jrtaylor71/ESP32-DevKitC3-Simple-Thermostat-PCB/SCHEDULE_SYNC_INDEX.md

# Schedule Sync Documentation Index

**Version 1.5.001** | Complete bidirectional MQTT schedule synchronization  
**Last Updated**: May 2026

Note: Schedule synchronization behavior remains compatible in v1.5.001. New US/EU regional HVAC controls are documented in README.md, DOCUMENTATION.md, and USER_MANUAL.md.

---

## 📖 Documentation Guide

### For Different Audiences

#### 👤 **I'm a First-Time User**
Start here for quickest setup:
1. [MQTT_SCHEDULE_QUICKSTART.md](MQTT_SCHEDULE_QUICKSTART.md) ⏱️ 5 minutes
   - Copy-paste setup commands
   - Verification checklist
   - Troubleshooting links

#### 👨‍💻 **I'm Setting Up Home Assistant**
Full user guide with detailed instructions:
1. [README.md § Home Assistant Integration](README.md#-home-assistant-integration)
   - Feature overview
   - Setup steps
   - Multi-device support

2. [USER_MANUAL.md § Schedule Synchronization](USER_MANUAL.md#schedule-synchronization-) 
   - Detailed setup (5 steps)
   - What gets created (helper breakdown)
   - How to edit schedules
   - Multi-thermostat guide

#### 🔧 **I'm a Developer/Integrator**
Technical deep-dive:
1. [DEVELOPMENT_GUIDE.md § MQTT 7-Day Schedule Architecture](DEVELOPMENT_GUIDE.md#mqtt-7-day-schedule-architecture-)
   - Firmware C++ structures
   - Inbound/outbound handlers
   - Day index conversion logic
   - HA automation code

2. [MQTT_SCHEDULE_SYNC.md](MQTT_SCHEDULE_SYNC.md)
   - Complete technical reference
   - All MQTT formats (topics, payloads)
   - Data flow diagrams
   - Advanced configuration

#### 🐛 **I'm Having Issues**
Problem-solving guide:
1. [MQTT_SCHEDULE_SYNC.md § Troubleshooting](MQTT_SCHEDULE_SYNC.md#troubleshooting)
   - 10+ common issues
   - Solutions for each
   - Debug commands
   - Verification steps

---

## 📚 Complete Documentation Map

### Core Documentation Files

| File | Size | Focus | Audience |
|---|---|---|---|
| [README.md](README.md) | 15K | Product overview, features, HA integration | Everyone |
| [USER_MANUAL.md](USER_MANUAL.md) | 40K | Complete user guide, all features | End users, installers |
| [DEVELOPMENT_GUIDE.md](DEVELOPMENT_GUIDE.md) | 29K | Architecture, code examples, extending | Developers |

### Schedule-Specific Documentation

| File | Size | Focus | For |
|---|---|---|-----|
| [MQTT_SCHEDULE_QUICKSTART.md](MQTT_SCHEDULE_QUICKSTART.md) | 2.3K | 5-min setup | New users |
| [MQTT_SCHEDULE_SYNC.md](MQTT_SCHEDULE_SYNC.md) | 18K | Complete technical reference | Developers, integrators |
| [DOCUMENTATION_UPDATE.md](DOCUMENTATION_UPDATE.md) | 7.8K | This update summary | Project managers |

---

## 🚀 Quick Navigation by Task

### "I want to set up schedule sync"
→ [MQTT_SCHEDULE_QUICKSTART.md](MQTT_SCHEDULE_QUICKSTART.md) (5 min)

### "I need detailed setup instructions"
→ [USER_MANUAL.md § Schedule Synchronization](USER_MANUAL.md#schedule-synchronization-)

### "I want to understand the architecture"
→ [MQTT_SCHEDULE_SYNC.md § Architecture](MQTT_SCHEDULE_SYNC.md#architecture)

### "I need to debug why it's not working"
→ [MQTT_SCHEDULE_SYNC.md § Troubleshooting](MQTT_SCHEDULE_SYNC.md#troubleshooting)

### "I want to add another thermostat"
→ [USER_MANUAL.md § Multi-Thermostat Support](USER_MANUAL.md#multi-thermostat-support)

### "I need to understand MQTT topics"
→ [MQTT_SCHEDULE_SYNC.md § MQTT Topics & Payloads](MQTT_SCHEDULE_SYNC.md#mqtt-topics--payloads)

### "I want to extend the system"
→ [MQTT_SCHEDULE_SYNC.md § Advanced Configuration](MQTT_SCHEDULE_SYNC.md#advanced-configuration)

### "I'm implementing custom automation"
→ [MQTT_SCHEDULE_SYNC.md § Integration with Automations](MQTT_SCHEDULE_SYNC.md#integration-with-automations)

---

## 📋 Key Topics Covered

### Setup & Installation
- [x] 5-minute quickstart
- [x] Step-by-step setup for HA
- [x] Multiple thermostat setup
- [x] Verification procedures

### Usage & Operation
- [x] Editing schedules in HA
- [x] Device-to-HA sync
- [x] HA-to-device sync
- [x] Helper organization

### Architecture & Implementation
- [x] MQTT topic formats
- [x] Payload specifications
- [x] Firmware implementation
- [x] HA automation design
- [x] Day index conversion (fix for v1.4.001)

### Troubleshooting
- [x] Helpers not appearing
- [x] Changes not syncing
- [x] Circular updates
- [x] Day off-by-one errors
- [x] MQTT connection issues
- [x] Wrong device responding

### Advanced Topics
- [x] Adding new devices
- [x] Custom automation integration
- [x] MQTT topic monitoring
- [x] Multi-thermostat scaling

---

## 🔢 By The Numbers

### Documentation Statistics
- **3,406 total lines** of documentation
- **6 markdown files** created/updated
- **571 lines** in MQTT schedule deep-dive
- **125 lines** added to USER_MANUAL
- **200 lines** added to DEVELOPMENT_GUIDE
- **50 lines** added to README

### System Specifications
- **77 helpers** per thermostat
- **77 outbound automations** per thermostat
- **1 centralized** inbound automation
- **Unlimited thermostats** support
- **0% manual config** (all generated)

### Coverage
- **10+** troubleshooting scenarios
- **7** MQTT topic formats documented
- **3** payload structure variations
- **5** setup instruction variants
- **4** day index edge cases explained

---

## ✨ What's New in v1.4.001

### Bidirectional Schedule Sync
- ✅ Device → HA (inbound) synchronization
- ✅ HA → Device (outbound) synchronization
- ✅ No circular updates or conflicts
- ✅ Instant sync (1-2 second latency)

### Multi-Thermostat Support
- ✅ Unlimited thermostat support
- ✅ Automatic hostname normalization
- ✅ Centralized multi-device automation
- ✅ Per-device helper isolation

### Fixed Day Index Bug
- ✅ Proper MQTT format (0=Monday)
- ✅ Firmware array format (0=Sunday)
- ✅ Automatic conversion at MQTT boundaries
- ✅ No more off-by-one errors

### Automation Generation
- ✅ Single-command package generation
- ✅ 77 automations per device
- ✅ 77 helpers per device
- ✅ All formats correct (JSON, booleans, times)

---

## 🎯 Recommended Reading Order

### For End Users
1. [README.md § Home Assistant Integration](README.md#-home-assistant-integration) (2 min)
2. [MQTT_SCHEDULE_QUICKSTART.md](MQTT_SCHEDULE_QUICKSTART.md) (5 min)
3. [USER_MANUAL.md § Schedule Synchronization](USER_MANUAL.md#schedule-synchronization-) (15 min)
4. [MQTT_SCHEDULE_SYNC.md § Troubleshooting](MQTT_SCHEDULE_SYNC.md#troubleshooting) (as needed)

### For Developers
1. [README.md](README.md) (5 min)
2. [DEVELOPMENT_GUIDE.md § MQTT 7-Day Schedule Architecture](DEVELOPMENT_GUIDE.md#mqtt-7-day-schedule-architecture-) (20 min)
3. [MQTT_SCHEDULE_SYNC.md](MQTT_SCHEDULE_SYNC.md) (30 min)
4. Source code in [Main-Thermostat.cpp](src/Main-Thermostat.cpp#L2968)

### For System Integrators
1. [MQTT_SCHEDULE_QUICKSTART.md](MQTT_SCHEDULE_QUICKSTART.md) (5 min)
2. [MQTT_SCHEDULE_SYNC.md § Setup Instructions](MQTT_SCHEDULE_SYNC.md#setup-instructions) (15 min)
3. [MQTT_SCHEDULE_SYNC.md § MQTT Topics & Payloads](MQTT_SCHEDULE_SYNC.md#mqtt-topics--payloads) (20 min)
4. [MQTT_SCHEDULE_SYNC.md § Advanced Configuration](MQTT_SCHEDULE_SYNC.md#advanced-configuration) (as needed)

---

## 🔗 Direct File Links

### Main Documentation
- [README.md](README.md) - Product overview and features
- [USER_MANUAL.md](USER_MANUAL.md) - Complete user guide
- [DEVELOPMENT_GUIDE.md](DEVELOPMENT_GUIDE.md) - Developer reference

### Schedule-Specific
- [MQTT_SCHEDULE_QUICKSTART.md](MQTT_SCHEDULE_QUICKSTART.md) - Quick start guide
- [MQTT_SCHEDULE_SYNC.md](MQTT_SCHEDULE_SYNC.md) - Technical reference
- [DOCUMENTATION_UPDATE.md](DOCUMENTATION_UPDATE.md) - Update summary

### Implementation Files
- [Main-Thermostat.cpp](src/Main-Thermostat.cpp) - Firmware code
- [multi_thermostat_schedule_sync.yaml](multi_thermostat_schedule_sync.yaml) - HA inbound automation
- [template_thermostat_schedule.yaml](template_thermostat_schedule.yaml) - HA outbound template
- [generate_schedule_package.sh](generate_schedule_package.sh) - Package generator script

---

## 📞 Support & Troubleshooting

### Getting Help
1. **Quick answer?** → [MQTT_SCHEDULE_QUICKSTART.md](MQTT_SCHEDULE_QUICKSTART.md)
2. **Setup help?** → [USER_MANUAL.md § Schedule Synchronization](USER_MANUAL.md#schedule-synchronization-)
3. **Troubleshooting?** → [MQTT_SCHEDULE_SYNC.md § Troubleshooting](MQTT_SCHEDULE_SYNC.md#troubleshooting)
4. **Technical details?** → [MQTT_SCHEDULE_SYNC.md](MQTT_SCHEDULE_SYNC.md)
5. **Code questions?** → [DEVELOPMENT_GUIDE.md](DEVELOPMENT_GUIDE.md)

### Common Issues

| Problem | Solution |
|---|---|
| Helpers not appearing | See [Troubleshooting § Helpers Not Appearing](MQTT_SCHEDULE_SYNC.md#helpers-not-appearing) |
| Changes not syncing | See [Troubleshooting § Changes Not Syncing](MQTT_SCHEDULE_SYNC.md#changes-not-syncing-device--ha) |
| Day off-by-one errors | See [Troubleshooting § Day Off-by-One Errors](MQTT_SCHEDULE_SYNC.md#day-off-by-one-errors) (Fixed in v1.4.001!) |
| MQTT connection issues | See [Troubleshooting § Connection Issues](MQTT_SCHEDULE_SYNC.md#common-issues) |

---

## 📊 Documentation Completeness Checklist

- ✅ Feature overview
- ✅ Quick start guide (5 minutes)
- ✅ Complete setup instructions
- ✅ User guide for end users
- ✅ Developer architecture guide
- ✅ Technical reference
- ✅ MQTT formats documented
- ✅ Troubleshooting guide
- ✅ Advanced configuration guide
- ✅ Code examples
- ✅ Multiple thermostat guide
- ✅ Integration with automation guide
- ✅ Version history
- ✅ References to source code

---

## 📝 Document Versions

| Document | v1.3.9 | v1.4.001 | Change |
|---|---|---|---|
| README.md | ✓ | ✓ | +50 lines |
| USER_MANUAL.md | ✓ | ✓ | +125 lines |
| DEVELOPMENT_GUIDE.md | ✓ | ✓ | +200 lines |
| MQTT_SCHEDULE_SYNC.md | ✗ | ✓ | NEW (571 lines) |
| MQTT_SCHEDULE_QUICKSTART.md | ✗ | ✓ | NEW (80 lines) |
| DOCUMENTATION_UPDATE.md | ✗ | ✓ | NEW (298 lines) |

---

## 🎓 Learning Path

**Beginner** (30 min total)
1. Read: [MQTT_SCHEDULE_QUICKSTART.md](MQTT_SCHEDULE_QUICKSTART.md) (5 min)
2. Setup: Follow 5 quick steps (10 min)
3. Verify: Confirm helpers appear (5 min)
4. Try: Edit one helper and verify sync (10 min)

**Intermediate** (1 hour total)
1. Read: [USER_MANUAL.md § Schedule Synchronization](USER_MANUAL.md#schedule-synchronization-) (20 min)
2. Setup: Full setup with multiple devices (20 min)
3. Explore: Verify all 77 helpers (10 min)
4. Integrate: Add to your automations (10 min)

**Advanced** (2+ hours)
1. Read: [MQTT_SCHEDULE_SYNC.md](MQTT_SCHEDULE_SYNC.md) (45 min)
2. Study: [DEVELOPMENT_GUIDE.md § MQTT Architecture](DEVELOPMENT_GUIDE.md#mqtt-7-day-schedule-architecture-) (30 min)
3. Review: Source code in [Main-Thermostat.cpp](src/Main-Thermostat.cpp) (30 min)
4. Extend: Implement custom features (30 min)

---

**Status**: Complete and Ready  
**Quality**: Production  
**Last Updated**: January 2026  
**Version**: 1.4.001
