jrtaylor71/ESP32-DevKitC3-Simple-Thermostat-PCB/src/Main-Thermostat.cpp

/* 
 * Firmware Implementation
 * Copyright (c) 2025 Jonn Taylor (jrtaylor@taylordatacom.com)
 * 
 * This firmware implementation provides enhanced features including:
 * - Option C centralized display management with FreeRTOS tasks
 * - Advanced multi-stage HVAC control with intelligent staging
 * - Home Assistant integration with proper temperature precision
 * - Comprehensive MQTT support with auto-discovery
 * - Web-based configuration interface
 * - Professional dual-core architecture for ESP32-S3
 *
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
 * You should have received a copy of the GNU General Public License
 * along with this program.  If not, see <https://www.gnu.org/licenses/>.
 */


#include <WiFi.h>
#include <ESPAsyncWebServer.h>
#include <Preferences.h>
#include <esp_netif.h>
#include <Wire.h>
#include <Adafruit_AHTX0.h>
#include <DHT.h>
#include <Adafruit_BME280.h>
#include <Adafruit_BME680.h>
#include <Adafruit_SHT4x.h>
#include "TFT_Setup_ESP32_S3_Thermostat.h"
#include <HTTPClient.h>
#include <PubSubClient.h> // Include the MQTT library
#include <esp_task_wdt.h> // Watchdog reset API used in main loop
#include <time.h>
#include <ArduinoJson.h> // Include the ArduinoJson library
#include <OneWire.h>
#include <MyLD2410.h> // LD2410 radar library
#include "WebInterface.h"
#include "WebPages.h"
#include <DallasTemperature.h>
#include <Update.h> // For OTA firmware update
#include "esp_heap_caps.h" // Heap diagnostics
#include "Weather.h" // Weather integration module
#include "driver/gpio.h" // GPIO driver for pin control
#include "driver/usb_serial_jtag.h" // USB Serial JTAG driver for proper disable
#include "hal/usb_serial_jtag_ll.h" // USB Serial JTAG low-level
#include "soc/rtc_cntl_reg.h" // RTC control registers
#include "soc/io_mux_reg.h" // IO MUX registers for pin function override
#include "esp_rom_gpio.h" // ROM GPIO functions
#include "HardwarePins.h" // Hardware pin definitions
#include "SettingsUI.h"

// Version control information
const String sw_version = "1.5.008"; // Software version - split heat/cool fan relay requirements + hydronic guard fix
const String build_date = __DATE__;  // Compile date
const String build_time = __TIME__;  // Compile time
String version_info = sw_version + " (" + build_date + " " + build_time + ")";

// Constants
const int SECONDS_PER_HOUR = 3600;

// Temperature/Humidity Sensor Configuration
enum SensorType {
    SENSOR_NONE = 0,
    SENSOR_AHT20 = 1,
    SENSOR_DHT11 = 2,
    SENSOR_BME280 = 3,
    SENSOR_BME680 = 4,
    SENSOR_SHT45 = 5
};

// Sensor instances (only one will be active based on auto-detection)
Adafruit_AHTX0 aht;
DHT dht(I2C_SCL_PIN, DHT11); // DHT11 uses GPIO35 (SCL pin) as data line
Adafruit_BME280 bme;
Adafruit_BME680 bme680;
Adafruit_SHT4x sht45;

// Active sensor tracking
SensorType activeSensor = SENSOR_NONE;
String sensorName = "None";
float currentPressure = 0.0; // Barometric pressure (BME280/BME680 only, in hPa)
float currentGasResistance = 0.0; // Gas resistance (BME680 only, in kOhms)
float currentAirQuality = 0.0; // Approximate air quality index (BME680 only, 0-500)

// Hardware pin definitions moved to HardwarePins.h
// BOOT_BUTTON, LD2410 pins, ONE_WIRE_BUS, LIGHT_SENSOR_PIN, TFT_BACKLIGHT_PIN all defined there

// Settings for factory reset
unsigned long bootButtonPressStart = 0; // When the boot button was pressed
bool bootButtonPressed = false; // Track if boot button is being pressed

// DS18B20 sensor setup (pin defined in HardwarePins.h as ONEWIRE_PIN)
// NOTE: Create as pointers and initialize AFTER GPIO41 USB JTAG disable in setup()
OneWire* oneWire = nullptr;
DallasTemperature* ds18b20 = nullptr;

// Store DS18B20 ROM addresses
uint8_t ds18b20Address1[8] = {0};
uint8_t ds18b20Address2[8] = {0};
bool ds18b20Address1Valid = false;
bool ds18b20Address2Valid = false;

float hydronicTemp = 0.0;
float hydronicReturnTemp = 0.0;
bool hydronicHeatingEnabled = false;

// Hydronic system settings
float hydronicTempLow = 110.0; // Default low temperature for hydronic heating
float hydronicTempHigh = 130.0; // Default high temperature for hydronic heating

// Hydronic alert tracking
bool hydronicLowTempAlertSent = false; // Track if low temp alert has been sent
unsigned long lastHydronicAlertTime = 0; // Track last alert time to prevent spam
bool hydronicLockout = false; // Track hydronic safety lockout state

// Light sensor and display dimming setup (PWM constants now in HardwarePins.h)
// LIGHT_SENSOR_PIN and TFT_BACKLIGHT_PIN are defined in HardwarePins.h
// PWM_CHANNEL, PWM_CHANNEL_HEAT, PWM_CHANNEL_COOL, PWM_CHANNEL_FAN, PWM_CHANNEL_BUZZER defined in HardwarePins.h
// PWM_FREQ and PWM_RESOLUTION defined in HardwarePins.h
int lastLightReading = 0; // Last light sensor reading
unsigned long lastBrightnessUpdate = 0; // Last time brightness was updated
int currentBrightness = MAX_BRIGHTNESS; // Current backlight brightness
float filteredBrightness = 255.0; // EMA-filtered brightness for smooth transitions
const float brightnessEMAAlpha = 0.2; // Brightness smoothing factor (0.2 = 20% new, 80% previous)
bool ldrDimmingEnabled = false; // Enable/disable LDR-based dimming
// Display sleep mode settings
bool displaySleepEnabled = false; // Enable/disable display sleep mode
unsigned long displaySleepTimeout = 300000; // Sleep after 5 minutes (300000ms) of inactivity
bool displayIsAsleep = false; // Current display sleep state
unsigned long lastInteractionTime = 0; // Last time user interacted with display
unsigned long lastWakeTime = 0; // Last time display woke from sleep

// Motion sensor variables
MyLD2410 radar(Serial2);
bool motionDetected = false;
unsigned long lastMotionTime = 0;
bool ld2410Connected = false;
bool motionWakeEnabled = true; // Disable until sensor configuration verified working (disabled due to false positives)
unsigned long lastSleepTime = 0; // Last time display went to sleep
unsigned long radarDataTimestamp = 0; // Timestamp when radar data was last updated by readMotionSensor()
const unsigned long MOTION_WAKE_COOLDOWN = 5000; // Don't wake from motion for 5 seconds after sleep
const unsigned long MOTION_WAKE_DEBOUNCE = 2000; // Require 2 seconds of sustained motion to filter brief blips
const int MOTION_WAKE_MAX_DISTANCE = 100; // Only wake on motion within 100cm (close range only)
const unsigned long RADAR_DATA_MAX_AGE = 500; // Consider radar data stale after 500ms
const int MOTION_WAKE_MIN_SIGNAL = 50; // Minimum signal strength - increased to filter noise
const int MOTION_WAKE_MAX_SIGNAL = 100; // Maximum signal

// Weather integration settings
int weatherSource = 0; // 0=disabled, 1=OpenWeatherMap, 2=HomeAssistant
String owmApiKey = "";
String owmCity = "";
String owmState = "";
String owmCountry = "";
String haUrl = "";
String haToken = "";
String haEntityId = "";
int weatherUpdateInterval = 5; // Update interval in minutes (default 5)
Weather weather; // Weather object

// Hybrid staging settings
unsigned long stage1MinRuntime = 300; // Default minimum runtime for first stage in seconds (5 minutes)
float stage2TempDelta = 2.0; // Default temperature delta for second stage activation
unsigned long stage1StartTime = 0; // Time when stage 1 was activated
unsigned long stage2StartTime = 0; // Time when stage 2 was activated (for min runtime tracking)
const unsigned long STAGE2_MIN_RUNTIME = 60000; // Minimum 60 seconds before stage 2 can deactivate
bool stage1Active = false; // Flag to track if stage 1 is active
bool stage2Active = false; // Flag to track if stage 2 is active
bool stage2HeatingEnabled = false; // Enable/disable 2nd stage heating
bool stage2CoolingEnabled = false; // Enable/disable 2nd stage cooling
bool reversingValveEnabled = false; // Enable reversing valve (heat pump) - mutually exclusive with stage2HeatingEnabled

// Backup heat settings
// relay: 0=PUMP relay, 1=HEAT relay 2 (stage 2 heat), 2=COOL relay 2 (stage 2 cool output)
bool backupHeatEnabled = false;
int backupHeatRelaySelection = 0;
int backupHeatDelayMinutes = 30;
float backupHeatMinTempRise = 0.5f;
float backupHeatMaxTempDrop = 1.5f;
bool backupHeatActive = false;
unsigned long backupHeatDemandStart = 0;
unsigned long backupHeatLastTempRiseTime = 0;
float backupHeatLastReferenceTemp = NAN;

// US/EU Mode and Humidity Control Settings
// region: "US" or "EU"
String thermostatRegion = "US";
// EU-specific humidity dehumidification settings
// relay: 0=COOL relay 1 (default), 1=COOL relay 2 (stage 2 cool), 2=PUMP relay
bool euHumidityControlEnabled = false;
int euHumidityRelaySelection = 0;
float euHumiditySetpoint = 60.0f;  // Target humidity % (activate dehumidification above this)
float euHumidityDeadband = 5.0f;   // Hysteresis deadband for humidity control
bool euHumidityDemandActive = false;

// Globals
AsyncWebServer server(80);
LGFX tft;
DisplayVariant activeDisplay = DISPLAY_ILI9341;  // updated at boot by tft.initDisplay()
WiFiClient espClient;
PubSubClient mqttClient(espClient); // Initialize the MQTT client
Preferences preferences; // Preferences instance
String inputText = "";
bool isEnteringSSID = true;

// Add a new global flag to track WiFi setup mode
bool inWiFiSetupMode = false;

// Keyboard context to reuse keypad for WiFi and hostname entry (enum in SettingsUI.h)
KeyboardMode keyboardMode = KB_WIFI_SSID;
bool keyboardReturnToSettings = false;

// Settings UI state
bool inSettingsMenu = false;

// Keyboard layout constants
const char* KEYBOARD_UPPER[5][10] = {
    {"1", "2", "3", "4", "5", "6", "7", "8", "9", "0"},
    {"Q", "W", "E", "R", "T", "Y", "U", "I", "O", "P"},
    {"A", "S", "D", "F", "G", "H", "J", "K", "L", "DEL"},
    {"Z", "X", "C", "V", "B", "N", "M", "SPC", "CLR", "OK"},
    {"!", "@", "#", "$", "_", "-", "&", "*", ")", "SHIFT"}
};

const char* KEYBOARD_LOWER[5][10] = {
    {"1", "2", "3", "4", "5", "6", "7", "8", "9", "0"},
    {"q", "w", "e", "r", "t", "y", "u", "i", "o", "p"},
    {"a", "s", "d", "f", "g", "h", "j", "k", "l", "DEL"},
    {"z", "x", "c", "v", "b", "n", "m", "SPC", "CLR", "OK"},
    {"!", "@", "#", "$", "%", "^", "&", "*", "(", "SHIFT"}
};

// Keyboard layout constants
const int KEY_WIDTH = 27;
const int KEY_HEIGHT = 28;
const int KEY_SPACING = 2;
const int KEYBOARD_X_OFFSET = 15;
const int KEYBOARD_Y_OFFSET = 75;

// UI scaling helpers: keep layout logic in 320x240 virtual space and scale at draw time.
static inline int uiScaleX(int x) { return (x * dispW()) / 320; }
static inline int uiScaleY(int y) { return (y * dispH()) / 240; }
static inline int uiUnscaleX(int x) { return (x * 320) / dispW(); }
static inline int uiUnscaleY(int y) { return (y * 240) / dispH(); }

// Dual-core task handle
TaskHandle_t sensorTask;

// GPIO pin definitions moved to HardwarePins.h for centralized hardware abstraction

// Settings
float setTempHeat = 72.0; // Default set temperature for heating in Fahrenheit
float setTempCool = 76.0; // Default set temperature for cooling in Fahrenheit
float setTempAuto = 74.0; // Default set temperature for auto mode
float tempSwing = 1.0;
float autoTempSwing = 3.0;
bool fanRelayNeededHeat = false;
bool fanRelayNeededCool = false;
bool useFahrenheit = true; // Default to Fahrenheit
bool mqttEnabled = false; // Default to MQTT disabled
String wifiSSID = "";
String wifiPassword = "";
int fanMinutesPerHour = 15;                                                                     // Default to 15 minutes per hour
unsigned long lastFanRunTime = 0;                                                               // Time when the fan last ran
unsigned long fanRunDuration = 0;                                                               // Duration for which the fan has run in the current hour
const float tempDifferential = 4.0; // Fixed differential between heat and cool for auto changeover
bool use24HourClock = true; // Default to 24-hour clock

// MQTT settings
String mqttServer = "0.0.0.0"; // Replace with your MQTT server
int mqttPort = 1883;                    // Replace with your MQTT port
String mqttUsername = "mqtt";  // Replace with your MQTT username
String mqttPassword = "password";  // Replace with your MQTT password
String timeZone = "CST6CDT,M3.2.0,M11.1.0"; // Default time zone (Central Standard Time)

// Add a preference for hostname
String hostname = DEFAULT_HOSTNAME; // Default hostname via ProjectConfig

// Shower Mode settings
bool showerModeEnabled = false; // Master enable/disable for shower mode feature
int showerModeDuration = 30; // Duration in minutes (default 30)
bool showerModeActive = false;
unsigned long showerModeStartTime = 0;

// Modern Material Design Color Scheme
#define COLOR_BACKGROUND   0x1082    // Dark Gray #121212
#define COLOR_PRIMARY      0x1976    // Soft Blue #1976D2
#define COLOR_SECONDARY    0x0497    // Teal #0097A7
#define COLOR_ACCENT       0xFFC1    // Amber #FFC107
#define COLOR_TEXT         0xFFFF    // White #FFFFFF
#define COLOR_TEXT_LIGHT   0xE0E0    // Light Gray #E0E0E0
#define COLOR_SUCCESS      0x4CAF    // Soft Green #4CAF50
#define COLOR_WARNING      0xFF70    // Warm Orange #FF7043
#define COLOR_SURFACE      0x2124    // Slightly lighter gray #212121


bool heatingOn = false;
bool coolingOn = false;
bool fanOn = false;
String thermostatMode = "off"; // Default thermostat mode
String fanMode = "auto"; // Default fan mode

// 7-Day Scheduling System (structures defined in WebPages.h)
DaySchedule weekSchedule[7] = {
    // Sunday
    {{6, 0, 72.0, 76.0, 74.0, true}, {22, 0, 68.0, 78.0, 73.0, true}, true},
    // Monday
    {{6, 0, 72.0, 76.0, 74.0, true}, {22, 0, 68.0, 78.0, 73.0, true}, true},
    // Tuesday
    {{6, 0, 72.0, 76.0, 74.0, true}, {22, 0, 68.0, 78.0, 73.0, true}, true},
    // Wednesday
    {{6, 0, 72.0, 76.0, 74.0, true}, {22, 0, 68.0, 78.0, 73.0, true}, true},
    // Thursday
    {{6, 0, 72.0, 76.0, 74.0, true}, {22, 0, 68.0, 78.0, 73.0, true}, true},
    // Friday
    {{6, 0, 72.0, 76.0, 74.0, true}, {22, 0, 68.0, 78.0, 73.0, true}, true},
    // Saturday
    {{6, 0, 72.0, 76.0, 74.0, true}, {22, 0, 68.0, 78.0, 73.0, true}, true}
};

bool scheduleEnabled = false;        // Master schedule enable/disable
bool scheduleOverride = false;       // Temporary override active
const unsigned long scheduleOverrideDuration = 120; // Override duration in minutes (2 hours)
unsigned long overrideEndTime = 0;   // When override expires (0 = permanent)
String activePeriod = "manual";      // Current active period: "day", "night", "manual"
bool scheduleUpdatedFlag = false;    // Flag to indicate schedule needs to be saved

// AHT20 sensor calibration offsets
float tempOffset = 0.0; // Temperature offset in degrees (add to reading)
float humidityOffset = 0.0; // Humidity offset in % (add to reading)

// Add these declarations at the beginning of the file or in the appropriate section for global variables
bool settingsChanged = false;
bool mqttCallbackActive = false;
unsigned long lastMQTTMessageTime = 0;
const unsigned long mqttDebounceTime = 1000; // 1 second debounce time

bool tempHeatChanged = false;
bool tempCoolChanged = false;
bool tempSwingChanged = false;
bool thermostatModeChanged = false;
bool fanModeChanged = false;
bool handlingMQTTMessage = false; // Add this flag

// Mode switch debounce/delay (prevent rapid mode switching)
const unsigned long MODE_SWITCH_DELAY_MS = 3000; // 3 second delay between mode switches (except to OFF)
unsigned long lastModeSwitchTime = 0; // Track when the last mode switch occurred

// Force a full display redraw (clears cached values)
bool forceFullDisplayRefresh = false;

// Add declarations to support hydronic temperature display and sensor error checking
float previousHydronicTemp = 0.0;
float previousHydronicReturnTemp = 0.0;
bool ds18b20SensorPresent = false;
bool ds18b20ReturnSensorPresent = false;

// Function prototypes
void setupWiFi();
void controlRelays(float currentTemp);
void handleWebRequests();
void updateDisplay(float currentTemp, float currentHumidity);
void saveSettings();
void loadSettings();
void setupMQTT();
void reconnectMQTT();
float convertCtoF(float celsius);
void controlFanSchedule();
void saveWiFiSettings();
void drawKeyboard(bool isUpperCaseKeyboard);
void handleKeyPress(int row, int col);
void drawButtons();
void handleButtonPress(uint16_t x, uint16_t y);
void handleKeyboardTouch(uint16_t x, uint16_t y, bool isUpperCaseKeyboard);
void connectToWiFi();
void handleWiFiConnectionState(unsigned long currentTime);
void enterWiFiCredentials();
void calibrateTouchScreen();
void runInteractiveCalibration();
void clearTouchCalibration();
void startWiFiSetupUI(bool returnToSettings);
void exitKeyboardToPreviousScreen();
void restoreDefaultSettings();
void mqttCallback(char* topic, byte* payload, unsigned int length);
void sendMQTTData();
void resetMQTTDataCache(); // Force republish all MQTT data on next sendMQTTData call
void readLightSensor();
void updateDisplayBrightness();

// Schedule function prototypes
void checkSchedule();
void applySchedule(int dayOfWeek, bool isDayPeriod);
void saveScheduleSettings();
void loadScheduleSettings();
String getCurrentPeriod();
int getCurrentDayOfWeek();
void setBrightness(int brightness);
float getCalibratedTemperature(float rawTemp);
float getCalibratedHumidity(float rawHumidity);
void checkDisplaySleep();
void wakeDisplay();
void sleepDisplay();
bool testLD2410Connection();
bool configureLD2410Sensitivity();
void readMotionSensor();
void updateStatusLEDs();
void setHeatLED(bool state);
void setCoolLED(bool state);
void setFanLED(bool state);
void buzzerBeep(int duration = 125);
void buzzerStartupTone();
void publishHomeAssistantDiscovery();
void turnOffAllRelays();
void activateHeating();
void activateCooling();
void handleFanControl();
void enforceBackupHeatRelayConflicts();
void enforceEUHumidityRelayConflicts();
int getBackupHeatRelayPin();
void setBackupHeatRelay(bool enabled);
void clearBackupHeatState(const char* reason);
void updateBackupHeatState(bool heatDemandActive, float currentTemp);

// Sensor abstraction function prototypes
SensorType detectSensor();
bool initializeSensor(SensorType sensor);
bool readTemperatureHumidity(float &temp, float &humidity, float &pressure);

// Option C - Centralized Display Update System
void displayUpdateTaskFunction(void* parameter);
void updateDisplayIndicators();
void setDisplayUpdateFlag();
TaskHandle_t displayUpdateTask = NULL;
bool displayUpdateRequired = false;
unsigned long displayUpdateInterval = 500; // Update every 500ms
SemaphoreHandle_t displayUpdateMutex = NULL;
SemaphoreHandle_t controlRelaysMutex = NULL;
SemaphoreHandle_t radarSensorMutex = NULL;
SemaphoreHandle_t i2cMutex = NULL; // Protect I2C bus access (AHT20 sensor)
SemaphoreHandle_t nvsSaveMutex = NULL; // Protect NVS/preferences save operations (dual-core safety)

// Diagnostics
void logRuntimeDiagnostics();

// Display indicator states (managed centrally)
struct DisplayIndicators {
    bool heatIndicator = false;
    bool coolIndicator = false;
    bool fanIndicator = false;
    bool autoIndicator = false;
    bool stage1Indicator = false;
    bool stage2Indicator = false;
    unsigned long lastUpdate = 0;
} displayIndicators;

uint16_t calibrationData[5] = { 300, 3700, 300, 3700, 7 }; // Example calibration data

float currentTemp = 0.0;
float currentHumidity = 0.0;
bool isUpperCaseKeyboard = true;
float previousTemp = 0.0;
float previousHumidity = 0.0;
float previousSetTemp = 0.0;
float previousMainDisplayTemp = NAN;
float previousSidebarSetTemp = NAN;
bool previousMainShowSetTemp = false;
bool showSetTempOnMainDisplay = false;
unsigned long showSetTempUntil = 0;
const unsigned long SETPOINT_DISPLAY_TIMEOUT_MS = 15000;
// bool firstHourAfterBoot = true; // Flag to track the first hour after bootup - DISABLED
volatile bool mqttFeedbackNeeded = false; // Flag for immediate MQTT feedback on settings change
bool wifiWasConnected = false; // Track WiFi state transitions for reconnect handling
bool timeSyncInitialized = false; // Track one-time NTP init after first WiFi connect

// MQTT state tracking variables (moved from sendMQTTData to allow reset on reconnect)
float mqttLastTemp = 0.0;
float mqttLastHumidity = 0.0;
float mqttLastSetTempHeat = 0.0;
float mqttLastSetTempCool = 0.0;
float mqttLastSetTempAuto = 0.0;
String mqttLastThermostatMode = "";
String mqttLastFanMode = "";
String mqttLastAction = "";

// Temperature and humidity filtering (exponential moving average)
float filteredTemp = 0.0;              // EMA-filtered temperature
float filteredHumidity = 0.0;          // EMA-filtered humidity
const float tempEMAAlpha = 0.1;        // Temperature smoothing factor (0.1 = 10% new, 90% previous)
const float humidityEMAAlpha = 0.15;   // Humidity smoothing factor (0.15 = 15% new, 85% previous)
bool firstSensorReading = true;        // Flag to initialize filters on first read

// OTA progress tracking (server-side fallback)
volatile size_t otaBytesWritten = 0;      // Bytes written so far during current OTA
volatile size_t otaTotalSize = 0;         // Total size of firmware being uploaded
volatile bool otaInProgress = false;      // True while receiving firmware data
volatile bool otaRebooting = false;       // Set after successful end before reboot
volatile bool systemRebootInProgress = false; // Prevent multiple reboot requests
unsigned long otaStartTime = 0;           // millis() when OTA began
unsigned long otaLastUpdateLog = 0;       // For throttled serial logging

// Sensor task watchdog: updated each time the sensor task completes a control cycle.
// Main loop checks this and forces relays off if it stalls too long.
volatile unsigned long sensorTaskLastAlive = 0;

// Sensor reading task (runs on core 1)
void sensorTaskFunction(void *parameter) {
    unsigned long lastSensorError = 0;
    const unsigned long SENSOR_ERROR_COOLDOWN = 30000; // 30 second cooldown between reinits
    
    for (;;) {
        // Read sensor every 60 seconds to minimize processing load
        float tempReading, humidityReading, pressureReading;
        
        // Try to read sensor using abstraction layer
        bool readSuccess = readTemperatureHumidity(tempReading, humidityReading, pressureReading);
        
        if (!readSuccess) {
            debugLog("[SENSOR] Read failed!\n");
            
            // Try to reinitialize if cooldown has passed
            unsigned long now = millis();
            if (now - lastSensorError > SENSOR_ERROR_COOLDOWN) {
                debugLog("[SENSOR] Attempting %s reinit...\n", sensorName.c_str());
                if (initializeSensor(activeSensor)) {
                    debugLog("[SENSOR] %s reinitialized successfully\n", sensorName.c_str());
                } else {
                    debugLog("[SENSOR] %s reinit failed\n", sensorName.c_str());
                }
                lastSensorError = now;
            }
            vTaskDelay(pdMS_TO_TICKS(60000));
            continue;
        }
        
        // Apply calibration offsets
        float calibratedTemp = getCalibratedTemperature(tempReading);
        float calibratedHumidity = getCalibratedHumidity(humidityReading);
        
        float newTemp = useFahrenheit ? (calibratedTemp * 9.0 / 5.0 + 32.0) : calibratedTemp;
        float newHumidity = calibratedHumidity;
        
        // Update globals if valid
        if (!isnan(newTemp) && !isnan(newHumidity)) {
            // Apply exponential moving average filtering for smoother readings
            if (firstSensorReading) {
                filteredTemp = newTemp;
                filteredHumidity = newHumidity;
                firstSensorReading = false;
            } else {
                // EMA filter: smoothed_value = alpha * new_value + (1 - alpha) * previous_value
                filteredTemp = (tempEMAAlpha * newTemp) + ((1.0 - tempEMAAlpha) * filteredTemp);
                filteredHumidity = (humidityEMAAlpha * newHumidity) + ((1.0 - humidityEMAAlpha) * filteredHumidity);
            }
            
            currentTemp = filteredTemp;
            currentHumidity = filteredHumidity;
            
            // Update pressure if BME280/BME680 sensor and valid reading
            if ((activeSensor == SENSOR_BME280 || activeSensor == SENSOR_BME680) && !isnan(pressureReading)) {
                currentPressure = pressureReading;
            }
        }
        
        // Read DS18B20 hydronic temperature sensors if present
        if (ds18b20SensorPresent || ds18b20ReturnSensorPresent) {
            ds18b20->requestTemperatures();
            delay(750);  // Wait for temperature conversion (750ms for 12-bit resolution)

            if (ds18b20SensorPresent) {
                float hydTempC = ds18b20->getTempCByIndex(0);
                if (hydTempC != DEVICE_DISCONNECTED_C && hydTempC != -127.0 && !isnan(hydTempC)) {
                    // Valid reading - convert to Fahrenheit if needed
                    hydronicTemp = useFahrenheit ? (hydTempC * 9.0 / 5.0 + 32.0) : hydTempC;
                } else {
                    // Invalid reading - keep last valid reading, don't update
                    debugLog("[WARNING] DS18B20 supply sensor reading failed or disconnected\n");
                }
            }

            if (ds18b20ReturnSensorPresent) {
                float returnTempC = ds18b20->getTempCByIndex(1);
                if (returnTempC != DEVICE_DISCONNECTED_C && returnTempC != -127.0 && !isnan(returnTempC)) {
                    hydronicReturnTemp = useFahrenheit ? (returnTempC * 9.0 / 5.0 + 32.0) : returnTempC;
                } else {
                    debugLog("[WARNING] DS18B20 return sensor reading failed or disconnected\n");
                }
            }
        }
        
        // Control HVAC relays
        controlRelays(currentTemp);
        sensorTaskLastAlive = millis(); // Heartbeat: sensor task is alive
        
        // 5 second delay for responsive control while minimizing CPU load
        vTaskDelay(5000 / portTICK_PERIOD_MS);
    }
}

// Option C: Centralized Display Update Task
void displayUpdateTaskFunction(void* parameter) {
    debugLog("DISPLAY_TASK: Starting centralized display update task\n");
    
    for (;;) {
        // Check if display update is required or if enough time has passed
        bool updateNeeded = false;
        unsigned long currentTime = millis();
        
        if (xSemaphoreTake(displayUpdateMutex, pdMS_TO_TICKS(10)) == pdTRUE) {
            updateNeeded = displayUpdateRequired || 
                          (currentTime - displayIndicators.lastUpdate > displayUpdateInterval);
            
            if (updateNeeded) {
                if (displayUpdateRequired) {
                    debugLog("[DISPLAY_TASK] Flag-triggered update\n");
                } else {
                    debugLog("[DISPLAY_TASK] Timer-triggered update\n");
                }
                displayUpdateRequired = false;  // Clear the flag
                displayIndicators.lastUpdate = currentTime;
            }
            
            xSemaphoreGive(displayUpdateMutex);
        }
        
        if (updateNeeded) {
            updateDisplayIndicators();
        }
        
        // Run every 50ms to be responsive, but only update display when needed
        vTaskDelay(50 / portTICK_PERIOD_MS);
    }
}

// Update display indicators based on current system state
void updateDisplayIndicators() {
    debugLog("DISPLAY_UPDATE: Refreshing display indicators\n");
    
    // Take mutex to read system state safely
    if (xSemaphoreTake(displayUpdateMutex, pdMS_TO_TICKS(50)) == pdTRUE) {
        // Update indicator states based on current system state
        displayIndicators.heatIndicator = (thermostatMode == "heat") || 
                                         (thermostatMode == "auto" && heatingOn);
        displayIndicators.coolIndicator = (thermostatMode == "cool") || 
                                         (thermostatMode == "auto" && coolingOn);
        displayIndicators.fanIndicator = fanOn;
        displayIndicators.autoIndicator = (thermostatMode == "auto");
        displayIndicators.stage1Indicator = stage1Active;
        displayIndicators.stage2Indicator = stage2Active;
        
        xSemaphoreGive(displayUpdateMutex);
        
        // Update physical LED indicators (hardware I/O outside mutex)
        // LEDs show ACTIVE state (what's actually running), not just mode
        setHeatLED(heatingOn);
        setCoolLED(coolingOn);  
        setFanLED(fanOn);
        
        debugLog("DISPLAY_UPDATE: Heat=%s, Cool=%s, Fan=%s, Auto=%s, Stage1=%s, Stage2=%s\n",
             displayIndicators.heatIndicator ? "ON" : "OFF",
             displayIndicators.coolIndicator ? "ON" : "OFF",
             displayIndicators.fanIndicator ? "ON" : "OFF",
             displayIndicators.autoIndicator ? "ON" : "OFF",
             displayIndicators.stage1Indicator ? "ON" : "OFF",
             displayIndicators.stage2Indicator ? "ON" : "OFF");
    } else {
        debugLog("DISPLAY_UPDATE: Failed to take mutex, skipping update\n");
    }
}

// Function to request display update from other parts of the code
void setDisplayUpdateFlag() {
    if (xSemaphoreTake(displayUpdateMutex, pdMS_TO_TICKS(10)) == pdTRUE) {
        displayUpdateRequired = true;
        xSemaphoreGive(displayUpdateMutex);
        debugLog("[DISPLAY_FLAG_SET] Display update requested from controlRelays\n");
    } else {
        debugLog("[DISPLAY_FLAG_FAILED] Could not acquire mutex\n");
    }
}

// =============================================================================
// TEMPERATURE/HUMIDITY SENSOR ABSTRACTION LAYER
// =============================================================================

// Auto-detect which sensor is connected
SensorType detectSensor() {
    debugLog("[SENSOR] Starting sensor auto-detection...\n");
    
    // Initialize I2C bus first
    Wire.begin(I2C_SDA_PIN, I2C_SCL_PIN);
    delay(100);
    
    // Try BME680 first (has more features)
    debugLog("[SENSOR] Checking for BME680 at I2C address 0x76...\n");
    if (bme680.begin(0x76)) {
        debugLog("[SENSOR] BME680 detected at address 0x76!\n");
        return SENSOR_BME680;
    }
    
    debugLog("[SENSOR] Checking for BME680 at I2C address 0x77...\n");
    if (bme680.begin(0x77)) {
        debugLog("[SENSOR] BME680 detected at address 0x77!\n");
        return SENSOR_BME680;
    }
    
    // Try AHT20 (I2C address 0x38)
    debugLog("[SENSOR] Checking for AHT20 at I2C address 0x38...\n");
    if (aht.begin()) {
        debugLog("[SENSOR] AHT20 detected!\n");
        return SENSOR_AHT20;
    }
    
    // Try SHT45 (I2C address 0x44)
    debugLog("[SENSOR] Checking for SHT45 at I2C address 0x44...\n");
    if (sht45.begin(&Wire)) {
        debugLog("[SENSOR] SHT45 detected!\n");
        return SENSOR_SHT45;
    }
    
    // Try BME280 (I2C addresses 0x76 or 0x77)
    debugLog("[SENSOR] Checking for BME280 at I2C address 0x76...\n");
    if (bme.begin(0x76)) {
        debugLog("[SENSOR] BME280 detected at address 0x76!\n");
        return SENSOR_BME280;
    }
    
    debugLog("[SENSOR] Checking for BME280 at I2C address 0x77...\n");
    if (bme.begin(0x77)) {
        debugLog("[SENSOR] BME280 detected at address 0x77!\n");
        return SENSOR_BME280;
    }
    
    // No I2C sensor found, try DHT11 on GPIO35
    debugLog("[SENSOR] No I2C sensors found, trying DHT11...\n");
    debugLog("[SENSOR] Disabling I2C, switching GPIO35 to DHT11 mode...\n");
    Wire.end();
    pinMode(I2C_SCL_PIN, INPUT_PULLUP); // Configure GPIO35 as regular GPIO
    dht.begin();
    delay(2000); // DHT11 needs time to stabilize
    
    // Try reading from DHT11
    float testTemp = dht.readTemperature();
    float testHum = dht.readHumidity();
    
    if (!isnan(testTemp) && !isnan(testHum)) {
        debugLog("[SENSOR] DHT11 detected!\n");
        return SENSOR_DHT11;
    }
    
    debugLog("[SENSOR] ERROR: No temperature/humidity sensor detected!\n");
    return SENSOR_NONE;
}

// Initialize the detected sensor
bool initializeSensor(SensorType sensor) {
    debugLog("[SENSOR] Initializing %s sensor...\n", 
                  sensor == SENSOR_AHT20 ? "AHT20" : 
                  sensor == SENSOR_DHT11 ? "DHT11" : 
                  sensor == SENSOR_BME280 ? "BME280" :
                  sensor == SENSOR_BME680 ? "BME680" :
                  sensor == SENSOR_SHT45 ? "SHT45" : "NONE");
    
    switch(sensor) {
        case SENSOR_AHT20:
            Wire.begin(I2C_SDA_PIN, I2C_SCL_PIN);
            if (aht.begin()) {
                debugLog("[SENSOR] AHT20 initialized successfully\n");
                sensorName = "AHT20";
                return true;
            }
            debugLog("[SENSOR] AHT20 initialization failed\n");
            return false;
            
        case SENSOR_DHT11:
            Wire.end(); // Make sure I2C is disabled
            pinMode(I2C_SCL_PIN, INPUT_PULLUP);
            dht.begin();
            delay(2000);
            debugLog("[SENSOR] DHT11 initialized successfully\n");
            sensorName = "DHT11";
            return true;
            
        case SENSOR_BME280:
            Wire.begin(I2C_SDA_PIN, I2C_SCL_PIN);
            if (bme.begin(0x76) || bme.begin(0x77)) {
                // Configure BME280 for indoor monitoring
                bme.setSampling(Adafruit_BME280::MODE_NORMAL,
                               Adafruit_BME280::SAMPLING_X2,  // temperature
                               Adafruit_BME280::SAMPLING_X16, // pressure
                               Adafruit_BME280::SAMPLING_X1,  // humidity
                               Adafruit_BME280::FILTER_X16,
                               Adafruit_BME280::STANDBY_MS_500);
                debugLog("[SENSOR] BME280 initialized successfully\n");
                sensorName = "BME280";
                return true;
            }
            debugLog("[SENSOR] BME280 initialization failed\n");
            return false;
            
        case SENSOR_BME680:
            Wire.begin(I2C_SDA_PIN, I2C_SCL_PIN);
            if (bme680.begin(0x76) || bme680.begin(0x77)) {
                // Configure BME680 for indoor monitoring
                bme680.setTemperatureOversampling(BME680_OS_8X);
                bme680.setHumidityOversampling(BME680_OS_2X);
                bme680.setPressureOversampling(BME680_OS_4X);
                bme680.setIIRFilterSize(BME680_FILTER_SIZE_3);
                bme680.setGasHeater(320, 150); // 320°C heater temp, 150ms heating duration
                debugLog("[SENSOR] BME680 initialized successfully\n");
                sensorName = "BME680";
                return true;
            }
            debugLog("[SENSOR] BME680 initialization failed\n");
            return false;
            
        case SENSOR_SHT45:
            Wire.begin(I2C_SDA_PIN, I2C_SCL_PIN);
            if (sht45.begin(&Wire)) {
                sht45.setPrecision(SHT4X_HIGH_PRECISION);
                sht45.setHeater(SHT4X_NO_HEATER);
                debugLog("[SENSOR] SHT45 initialized successfully\n");
                sensorName = "SHT45";
                return true;
            }
            debugLog("[SENSOR] SHT45 initialization failed\n");
            return false;
    }
}

// Read temperature, humidity, and pressure from active sensor
bool readTemperatureHumidity(float &temp, float &humidity, float &pressure) {
    pressure = NAN; // Default to NAN for sensors without pressure
    
    switch(activeSensor) {
        case SENSOR_AHT20: {
            if (i2cMutex == NULL || xSemaphoreTake(i2cMutex, pdMS_TO_TICKS(100)) != pdTRUE) {
                return false;
            }
            
            sensors_event_t humidityEvent, tempEvent;
            bool success = aht.getEvent(&humidityEvent, &tempEvent);
            xSemaphoreGive(i2cMutex);
            
            if (success) {
                temp = tempEvent.temperature;
                humidity = humidityEvent.relative_humidity;
                return true;
            }
            return false;
        }
        
        case SENSOR_DHT11: {
            // DHT11 doesn't need mutex (not on I2C bus)
            temp = dht.readTemperature();
            humidity = dht.readHumidity();
            
            if (isnan(temp) || isnan(humidity)) {
                return false;
            }
            return true;
        }
        
        case SENSOR_BME280: {
            if (i2cMutex == NULL || xSemaphoreTake(i2cMutex, pdMS_TO_TICKS(100)) != pdTRUE) {
                return false;
            }
            
            temp = bme.readTemperature();
            humidity = bme.readHumidity();
            pressure = bme.readPressure() / 100.0F; // Convert Pa to hPa
            xSemaphoreGive(i2cMutex);
            
            if (isnan(temp) || isnan(humidity)) {
                return false;
            }
            return true;
        }
        
        case SENSOR_BME680: {
            if (i2cMutex == NULL || xSemaphoreTake(i2cMutex, pdMS_TO_TICKS(100)) != pdTRUE) {
                return false;
            }
            
            if (bme680.performReading()) {
                temp = bme680.temperature;
                humidity = bme680.humidity;
                pressure = bme680.pressure / 100.0F; // Convert Pa to hPa
                currentGasResistance = bme680.gas_resistance / 1000.0F; // Convert Ohms to kOhms
                
                // Simple air quality estimate based on gas resistance
                // Lower resistance = more volatile compounds = worse air quality
                // Baseline ~5-10 kOhm for clean air, ~0.5 kOhm for polluted air
                if (currentGasResistance > 0) {
                    // Scale 0.5-10 kOhm to 0-500 IAQ score
                    currentAirQuality = (currentGasResistance - 0.5) * (500.0 / (10.0 - 0.5));
                    currentAirQuality = constrain(currentAirQuality, 0, 500);
                } else {
                    currentAirQuality = 0;
                }
                
                xSemaphoreGive(i2cMutex);
                return true;
            }
            xSemaphoreGive(i2cMutex);
            return false;
        }
        
        case SENSOR_SHT45: {
            if (i2cMutex == NULL || xSemaphoreTake(i2cMutex, pdMS_TO_TICKS(100)) != pdTRUE) {
                return false;
            }
            
            sensors_event_t humidityEvent, tempEvent;
            bool success = sht45.getEvent(&humidityEvent, &tempEvent);
            xSemaphoreGive(i2cMutex);
            
            if (success) {
                temp = tempEvent.temperature;
                humidity = humidityEvent.relative_humidity;
                return true;
            }
            return false;
        }
        
        default:
            return false;
    }
}

// =============================================================================
// SCHEDULING SYSTEM FUNCTIONS
// =============================================================================

// Get current day of week (0 = Sunday, 1 = Monday, ..., 6 = Saturday)
int getCurrentDayOfWeek() {
    time_t now;
    struct tm timeinfo;
    time(&now);
    localtime_r(&now, &timeinfo);
    return timeinfo.tm_wday;
}

// Get current period description
String getCurrentPeriod() {
    if (!scheduleEnabled) return "manual";
    if (scheduleOverride) return "override";
    return activePeriod;
}

// Check if we need to apply a scheduled temperature change
void checkSchedule() {
    if (!scheduleEnabled) return;
    
    // Ensure timezone is applied
    tzset();
    
    // Get current time
    time_t now;
    struct tm timeinfo;
    time(&now);
    localtime_r(&now, &timeinfo);
    
    int currentHour = timeinfo.tm_hour;
    int currentMinute = timeinfo.tm_min;
    int currentDayOfWeek = timeinfo.tm_wday;
    
    // Debug: Log current time and schedule status
    static unsigned long lastDebugLog = 0;
    if (millis() - lastDebugLog > 60000) { // Log every 60 seconds
        debugLog("SCHEDULE DEBUG: Current time: %02d:%02d (day %d), TZ: %s, Period: %s\n", 
                 currentHour, currentMinute, currentDayOfWeek, timeZone.c_str(), activePeriod.c_str());
        lastDebugLog = millis();
    }
    bool overrideExpired = false;
    
    // Check if override has expired
    if (scheduleOverride && overrideEndTime > 0 && millis() >= overrideEndTime) {
        scheduleOverride = false;
        overrideEndTime = 0;
        overrideExpired = true;
        debugLog("SCHEDULE: Override expired, resuming schedule\n");
    }
    
    // Skip if override is active
    if (scheduleOverride) return;
    
    // Skip if this day is not enabled
    if (!weekSchedule[currentDayOfWeek].enabled) return;
    
    DaySchedule& today = weekSchedule[currentDayOfWeek];
    
    // Convert current time to minutes for easier comparison
    int currentMinutes = currentHour * 60 + currentMinute;
    int dayMinutes = today.day.hour * 60 + today.day.minute;
    int nightMinutes = today.night.hour * 60 + today.night.minute;
    
    // Determine which period we should be in
    String newPeriod = "manual";
    bool shouldApplyDaySchedule = false;
    bool shouldApplyNightSchedule = false;
    
    if (dayMinutes <= nightMinutes) {
        // Normal case: day < night (e.g., 6:00 AM - 10:00 PM)
        if (currentMinutes >= dayMinutes && currentMinutes < nightMinutes) {
            newPeriod = "day";
            shouldApplyDaySchedule = true;
        } else {
            newPeriod = "night";
            shouldApplyNightSchedule = true;
        }
    } else {
        // Cross-midnight case: night < day (e.g., 10:00 PM - 6:00 AM next day)
        if (currentMinutes >= dayMinutes || currentMinutes < nightMinutes) {
            newPeriod = "day";
            shouldApplyDaySchedule = true;
        } else {
            newPeriod = "night";
            shouldApplyNightSchedule = true;
        }
    }
    
    // Apply schedule if period changed or an override just ended
    bool shouldApplySchedule = overrideExpired || (newPeriod != activePeriod);
    if (shouldApplySchedule) {
        activePeriod = newPeriod;
        if (shouldApplyDaySchedule && today.day.active) {
            applySchedule(currentDayOfWeek, true);
        } else if (shouldApplyNightSchedule && today.night.active) {
            applySchedule(currentDayOfWeek, false);
        }
    }
}

// Apply scheduled temperatures
void applySchedule(int dayOfWeek, bool isDayPeriod) {
    DaySchedule& schedule = weekSchedule[dayOfWeek];
    SchedulePeriod& period = isDayPeriod ? schedule.day : schedule.night;
    
    if (!period.active) return;
    
    // Apply temperatures
    setTempHeat = period.heatTemp;
    setTempCool = period.coolTemp;
    setTempAuto = period.autoTemp;
    
    debugLog("SCHEDULE: Applied %s schedule for day %d - Heat: %.1f°F, Cool: %.1f°F, Auto: %.1f°F\n", 
                  isDayPeriod ? "day" : "night", dayOfWeek, setTempHeat, setTempCool, setTempAuto);
    
    // Save settings and update MQTT
    saveSettings();
    if (mqttEnabled && mqttClient.connected()) {
        mqttClient.publish("thermostat/setTempHeat", String(setTempHeat).c_str(), true);
        mqttClient.publish("thermostat/setTempCool", String(setTempCool).c_str(), true);
        mqttClient.publish("thermostat/activePeriod", activePeriod.c_str(), false);
    }
    
    // Update TFT display to show new scheduled temperature
    updateDisplay(currentTemp, currentHumidity);
    
    // Request display update for LED indicators
    setDisplayUpdateFlag();
}

// Save schedule settings to preferences
void saveScheduleSettings() {
    // Acquire mutex for atomic save operation (dual-core safety)
    if (nvsSaveMutex == NULL || xSemaphoreTake(nvsSaveMutex, pdMS_TO_TICKS(5000)) != pdTRUE) {
        debugLog("ERROR: saveScheduleSettings() timed out waiting for NVS mutex\n");
        return;
    }
    
    debugLog("SCHEDULE: Starting atomic save operation...\n");
    unsigned long saveStartTime = millis();
    
    preferences.putBool("schedEnabled", scheduleEnabled);
    preferences.putBool("schedOverride", scheduleOverride);
    preferences.putULong("overrideEnd", overrideEndTime);
    preferences.putString("activePeriod", activePeriod);
    
    // Save each day's schedule
    for (int day = 0; day < 7; day++) {
        String dayPrefix = "day" + String(day) + "_";
        
        preferences.putBool((dayPrefix + "enabled").c_str(), weekSchedule[day].enabled);
        
        // Day period
        preferences.putInt((dayPrefix + "d_hour").c_str(), weekSchedule[day].day.hour);
        preferences.putInt((dayPrefix + "d_min").c_str(), weekSchedule[day].day.minute);
        preferences.putFloat((dayPrefix + "d_heat").c_str(), weekSchedule[day].day.heatTemp);
        preferences.putFloat((dayPrefix + "d_cool").c_str(), weekSchedule[day].day.coolTemp);
        preferences.putFloat((dayPrefix + "d_auto").c_str(), weekSchedule[day].day.autoTemp);
        preferences.putBool((dayPrefix + "d_active").c_str(), weekSchedule[day].day.active);
        
        // Night period
        preferences.putInt((dayPrefix + "n_hour").c_str(), weekSchedule[day].night.hour);
        preferences.putInt((dayPrefix + "n_min").c_str(), weekSchedule[day].night.minute);
        preferences.putFloat((dayPrefix + "n_heat").c_str(), weekSchedule[day].night.heatTemp);
        preferences.putFloat((dayPrefix + "n_cool").c_str(), weekSchedule[day].night.coolTemp);
        preferences.putFloat((dayPrefix + "n_auto").c_str(), weekSchedule[day].night.autoTemp);
        preferences.putBool((dayPrefix + "n_active").c_str(), weekSchedule[day].night.active);
    }
    
    // Verify critical schedule settings were saved
    bool verifySuccess = true;
    bool verifySched = preferences.getBool("schedEnabled", !scheduleEnabled);
    
    if (verifySched != scheduleEnabled) {
        verifySuccess = false;
        debugLog("ERROR: Schedule verification FAILED—save may not have persisted!\n");
    } else {
        debugLog("SCHEDULE: Verification SUCCESS—schedule data confirmed in NVS\n");
    }
    
    unsigned long saveDuration = millis() - saveStartTime;
    debugLog("SCHEDULE: Atomic save completed in %lu ms (status=%s)\n", 
             saveDuration, verifySuccess ? "OK" : "FAILED");
    
    // Release mutex
    xSemaphoreGive(nvsSaveMutex);
}

// Load schedule settings from preferences
void loadScheduleSettings() {
    auto getOrInitBool = [&](const char* key, bool def) -> bool {
        if (!preferences.isKey(key)) {
            preferences.putBool(key, def);
            return def;
        }
        return preferences.getBool(key, def);
    };
    auto getOrInitULong = [&](const char* key, unsigned long def) -> unsigned long {
        if (!preferences.isKey(key)) {
            preferences.putULong(key, def);
            return def;
        }
        return preferences.getULong(key, def);
    };
    auto getOrInitString = [&](const char* key, const char* def) -> String {
        if (!preferences.isKey(key)) {
            preferences.putString(key, def);
            return String(def);
        }
        return preferences.getString(key, def);
    };

    scheduleEnabled = getOrInitBool("schedEnabled", false);
    scheduleOverride = getOrInitBool("schedOverride", false);
    overrideEndTime = getOrInitULong("overrideEnd", 0);
    activePeriod = getOrInitString("activePeriod", "manual");
    
    // If override was active before reboot, clear it since overrideEndTime is stale
    // (millis() resets to 0 after each reboot, making the stored endTime unreliable)
    if (scheduleOverride && overrideEndTime > 0) {
        debugLog("SCHEDULE: Clearing stale override from previous boot\n");
        scheduleOverride = false;
        overrideEndTime = 0;
    }
    
    // Check if schedule data exists, if not initialize defaults silently
    bool scheduleExists = preferences.isKey("day0_d_heat");
    if (!scheduleExists) {
        debugLog("SCHEDULE: First boot detected, initializing default schedule data...\n");
        saveScheduleSettings(); // Save the compiled-in defaults to NVS
        return; // Skip the individual loading since we just saved defaults
    }
    
    // Load each day's schedule with defaults
    for (int day = 0; day < 7; day++) {
        String dayPrefix = "day" + String(day) + "_";
        
        weekSchedule[day].enabled = preferences.getBool((dayPrefix + "enabled").c_str(), true);
        
        // Day period defaults (6:00 AM, 72°F heat, 76°F cool)
        weekSchedule[day].day.hour = preferences.getInt((dayPrefix + "d_hour").c_str(), 6);
        weekSchedule[day].day.minute = preferences.getInt((dayPrefix + "d_min").c_str(), 0);
        weekSchedule[day].day.heatTemp = preferences.getFloat((dayPrefix + "d_heat").c_str(), 72.0);
        weekSchedule[day].day.coolTemp = preferences.getFloat((dayPrefix + "d_cool").c_str(), 76.0);
        weekSchedule[day].day.autoTemp = preferences.getFloat((dayPrefix + "d_auto").c_str(), 74.0);
        weekSchedule[day].day.active = preferences.getBool((dayPrefix + "d_active").c_str(), true);
        
        // Night period defaults (10:00 PM, 68°F heat, 78°F cool)
        weekSchedule[day].night.hour = preferences.getInt((dayPrefix + "n_hour").c_str(), 22);
        weekSchedule[day].night.minute = preferences.getInt((dayPrefix + "n_min").c_str(), 0);
        weekSchedule[day].night.heatTemp = preferences.getFloat((dayPrefix + "n_heat").c_str(), 68.0);
        weekSchedule[day].night.coolTemp = preferences.getFloat((dayPrefix + "n_cool").c_str(), 78.0);
        weekSchedule[day].night.autoTemp = preferences.getFloat((dayPrefix + "n_auto").c_str(), 73.0);
        weekSchedule[day].night.active = preferences.getBool((dayPrefix + "n_active").c_str(), true);
    }
    
    debugLog("SCHEDULE: Settings loaded - Enabled: %s, Override: %s, Active Period: %s\n",
                  scheduleEnabled ? "YES" : "NO", 
                  scheduleOverride ? "YES" : "NO",
                  activePeriod.c_str());
}

// =============================================================================
// DEBUG LOG BUFFER - For web-based serial output viewing
// =============================================================================
const int DEBUG_BUFFER_SIZE = 65536;  // 64KB circular buffer for more history
char debugBuffer[DEBUG_BUFFER_SIZE];
int debugBufferIndex = 0;
bool debugBufferWrapped = false;  // Track if buffer has wrapped around
SemaphoreHandle_t debugBufferMutex = NULL;

void addToDebugBuffer(const char* message) {
    bool haveLock = false;
    if (debugBufferMutex != NULL) {
        haveLock = (xSemaphoreTake(debugBufferMutex, portMAX_DELAY) == pdTRUE);
    }
    
    int len = strlen(message);
    if (len > DEBUG_BUFFER_SIZE) len = DEBUG_BUFFER_SIZE;
    
    // Write to circular buffer
    for (int i = 0; i < len; i++) {
        debugBuffer[debugBufferIndex] = message[i];
        debugBufferIndex = (debugBufferIndex + 1) % DEBUG_BUFFER_SIZE;
        if (debugBufferIndex == 0) {
            debugBufferWrapped = true;  // We've wrapped around
        }
    }
    
    if (haveLock) {
        xSemaphoreGive(debugBufferMutex);
    }
}

String getDebugLog() {
    String result = "";
    bool haveLock = false;
    if (debugBufferMutex != NULL) {
        haveLock = (xSemaphoreTake(debugBufferMutex, portMAX_DELAY) == pdTRUE);
    }
    
    // Return only valid bytes in chronological order.
    int count = debugBufferWrapped ? DEBUG_BUFFER_SIZE : debugBufferIndex;
    int startIdx = debugBufferWrapped ? debugBufferIndex : 0;

    // When the circular buffer has wrapped, the oldest byte may be in the middle
    // of a log line. Advance to the next newline so the served log starts cleanly.
    if (debugBufferWrapped && count > 0) {
        int trim = 0;
        while (trim < count && debugBuffer[(startIdx + trim) % DEBUG_BUFFER_SIZE] != '\n') {
            trim++;
        }
        if (trim < count) {
            trim++; // skip the newline itself
            startIdx = (startIdx + trim) % DEBUG_BUFFER_SIZE;
            count -= trim;
        }
    }

    result.reserve(count + 16);
    for (int i = 0; i < count; i++) {
        int idx = (startIdx + i) % DEBUG_BUFFER_SIZE;
        result += debugBuffer[idx];
    }
    
    if (haveLock) {
        xSemaphoreGive(debugBufferMutex);
    }
    return result;
}

// Unified logging function for both Serial and debug buffer
void debugLog(const char* format, ...) {
    char buffer[256];
    va_list args;
    va_start(args, format);
    vsnprintf(buffer, sizeof(buffer), format, args);
    va_end(args);
    Serial.print(buffer);
    addToDebugBuffer(buffer);
}

void setup()
{
    // CRITICAL: GPIO41 is USB Serial JTAG D+ pin - must completely disable USB peripheral
    // Disable USB PHY entirely at hardware level (most aggressive method)
    REG_WRITE(RTC_CNTL_USB_CONF_REG, 0);  // Clear all USB config bits
    
    // Wait for USB peripheral to power down
    delay(100);
    
    // Force GPIO41 to GPIO function with strong configuration
    esp_rom_gpio_pad_select_gpio(41);
    PIN_FUNC_SELECT(GPIO_PIN_MUX_REG[41], PIN_FUNC_GPIO);
    
    // Configure pin: reset, then set as open-drain with pullup
    gpio_reset_pin((gpio_num_t)41);
    gpio_set_direction((gpio_num_t)41, GPIO_MODE_INPUT_OUTPUT_OD);
    gpio_set_pull_mode((gpio_num_t)41, GPIO_PULLUP_ONLY);
    gpio_pullup_en((gpio_num_t)41);
    gpio_pulldown_dis((gpio_num_t)41);
    
    // Explicitly drive pin high
    gpio_set_level((gpio_num_t)41, 1);
    
    delay(100);  // Allow pin to stabilize after all configuration;
    
    Serial.begin(115200);
    delay(100);  // Allow serial and GPIO41 to stabilize after USB JTAG disable
    
    // Initialize debug buffer with zeros and mutex
    memset(debugBuffer, 0, DEBUG_BUFFER_SIZE);
    debugBufferIndex = 0;
    debugBufferWrapped = false;
    
    // Initialize debug buffer mutex
    debugBufferMutex = xSemaphoreCreateMutex();
    if (debugBufferMutex == NULL) {
        debugLog("ERROR: Failed to create debug buffer mutex!\n");
    } else {
        debugLog("Debug buffer mutex created successfully\n");
        // Add initial message to buffer
        addToDebugBuffer("=== DEBUG BUFFER INITIALIZED ===\n");
    }

    // Initialize Preferences
    preferences.begin("thermostat", false);
    
    // Create NVS save semaphore for dual-core safety
    nvsSaveMutex = xSemaphoreCreateMutex();
    if (nvsSaveMutex == NULL) {
        debugLog("ERROR: Failed to create NVS save mutex!\n");
    }
    
    loadSettings();
    loadScheduleSettings();

    
    // Print version information at startup
    debugLog("\n");
    debugLog("========================================\n");
    debugLog("%s\n", PROJECT_NAME_SHORT);
    debugLog("Version: %s\n", sw_version.c_str());
    debugLog("Build Date: %s\n", build_date.c_str());
    debugLog("Build Time: %s\n", build_time.c_str());
    debugLog("Hostname: %s\n", hostname.c_str());
    debugLog("========================================\n");
    debugLog("\n");
    
    // Initialize the DHT11 sensor
    // Initialize TFT backlight with PWM (GPIO 14)
    ledcSetup(PWM_CHANNEL, PWM_FREQ, PWM_RESOLUTION);
    ledcAttachPin(TFT_BACKLIGHT_PIN, PWM_CHANNEL);
    // Start at saved brightness
    setBrightness(currentBrightness);
    filteredBrightness = currentBrightness; // Initialize EMA filter
    
    // Initialize light sensor pin
    pinMode(LIGHT_SENSOR_PIN, INPUT);
    
    // Initialize LD2410 motion sensor with pulldown to prevent floating
    pinMode(LD2410_MOTION_PIN, INPUT_PULLDOWN);
    // NOTE: Arduino Serial2.begin uses (baud, config, RX_pin, TX_pin) order
    // LD2410 TX (data out) connects to ESP32 RX (pin 15)
    // LD2410 RX (data in) connects to ESP32 TX (pin 16)
    Serial2.begin(256000, SERIAL_8N1, LD2410_RX_PIN, LD2410_TX_PIN);  // RX=15, TX=16
    delay(500); // Give sensor time to stabilize
    
    // Test LD2410 connection
    ld2410Connected = testLD2410Connection();
    if (ld2410Connected) {
        debugLog("LD2410: Motion sensor connected successfully\n");
        // Configure with conservative settings matching original hardware
        configureLD2410Sensitivity();
    } else {
        debugLog("LD2410: Motion sensor not detected - display control via touch only\n");
    }
    
    // Create I2C mutex BEFORE initializing I2C bus and devices
    i2cMutex = xSemaphoreCreateMutex();
    if (i2cMutex == NULL) {
        debugLog("ERROR: Failed to create I2C mutex!\n");
    } else {
        debugLog("I2C mutex created successfully\n");
    }
    
    // Auto-detect and initialize temperature/humidity sensor
    activeSensor = detectSensor();
    if (activeSensor != SENSOR_NONE) {
        if (!initializeSensor(activeSensor)) {
            debugLog("ERROR: Sensor initialization failed!\n");
            activeSensor = SENSOR_NONE;
            sensorName = "None";
        } else {
            debugLog("SUCCESS: %s sensor ready\n", sensorName.c_str());
        }
    } else {
        debugLog("ERROR: No temperature/humidity sensor detected!\n");
    }

    // Initialize the TFT display
    tft.initDisplay();  // detects panel, sets activeDisplay, calls init()+setRotation()
    tft.fillScreen(COLOR_BACKGROUND);
    tft.setTextColor(COLOR_TEXT, COLOR_BACKGROUND);
    tft.setTextSize(3);  // Increased size from 2 to 3
    tft.setCursor(15, 40);  // Better centered for display
    tft.println(PROJECT_NAME_SHORT);
    tft.setTextSize(2);  // Increased from 1 to 2 for better readability
    tft.setCursor(20, 110);  // Centered version info
    tft.println("Version: " + sw_version);
    tft.setCursor(25, 135);  // Centered build info
    tft.println("Build: " + build_date);
    tft.setCursor(40, 155);  // Centered build time
    tft.println("Time: " + build_time);
    tft.println();
    tft.setTextSize(2);
    delay(5000); // Allow time to read startup info
    tft.setCursor(60, 180);  // Center loading message
    tft.println("Loading Settings...");

    // Calibrate touch screen
    calibrateTouchScreen();

    // Initialize relay pins
    pinMode(HEAT_RELAY_1_PIN, OUTPUT);
    pinMode(HEAT_RELAY_2_PIN, OUTPUT);
    pinMode(COOL_RELAY_1_PIN, OUTPUT);
    pinMode(COOL_RELAY_2_PIN, OUTPUT);
    pinMode(FAN_RELAY_PIN, OUTPUT);

    // Initialize LED pins with PWM for dimmed operation
    ledcSetup(PWM_CHANNEL_HEAT, PWM_FREQ, PWM_RESOLUTION);
    ledcSetup(PWM_CHANNEL_COOL, PWM_FREQ, PWM_RESOLUTION);
    ledcSetup(PWM_CHANNEL_FAN, PWM_FREQ, PWM_RESOLUTION);
    ledcAttachPin(LED_HEAT_PIN, PWM_CHANNEL_HEAT);
    ledcAttachPin(LED_COOL_PIN, PWM_CHANNEL_COOL);
    ledcAttachPin(LED_FAN_PIN, PWM_CHANNEL_FAN);

    // Initialize buzzer with dedicated PWM channel
    ledcSetup(PWM_CHANNEL_BUZZER, 4000, PWM_RESOLUTION); // 4kHz for buzzer
    ledcAttachPin(BUZZER_PIN, PWM_CHANNEL_BUZZER);

    // Ensure all relays are off during bootup
    digitalWrite(HEAT_RELAY_1_PIN, LOW);
    digitalWrite(HEAT_RELAY_2_PIN, LOW);
    digitalWrite(COOL_RELAY_1_PIN, LOW);
    digitalWrite(COOL_RELAY_2_PIN, LOW);
    digitalWrite(FAN_RELAY_PIN, LOW);

    // Ensure all LEDs are off during bootup
    ledcWrite(PWM_CHANNEL_HEAT, 0);
    ledcWrite(PWM_CHANNEL_COOL, 0);
    ledcWrite(PWM_CHANNEL_FAN, 0);

    // Ensure buzzer is off during bootup
    ledcWrite(PWM_CHANNEL_BUZZER, 0);

    // Initialize WiFi in station mode to set up TCP/IP stack
    // This must be done before any WiFi operations (even WiFi.status() calls in loop)
    WiFi.mode(WIFI_STA);
    
    // Load WiFi credentials but don't force connection
    wifiSSID = preferences.getString("wifiSSID", "");
    wifiPassword = preferences.getString("wifiPassword", "");
    
    // Set hostname using ESP-IDF method (Arduino WiFi.setHostname has bugs)
    esp_netif_t* sta_netif = esp_netif_get_handle_from_ifkey("WIFI_STA_DEF");
    if (sta_netif != nullptr) {
        esp_err_t err = esp_netif_set_hostname(sta_netif, hostname.c_str());
        if (err != ESP_OK) {
            debugLog("[WIFI] Failed to set hostname: %d\n", err);
        } else {
            debugLog("[WIFI] Hostname set to: %s\n", hostname.c_str());
        }
    }
    WiFi.config(INADDR_NONE, INADDR_NONE, INADDR_NONE); // Force DHCP to send hostname
    
    // Clear the "Loading Settings..." message
    tft.fillScreen(COLOR_BACKGROUND);
    
    // Setup WiFi if credentials exist, but do not block startup if AP is unavailable
    if (wifiSSID != "" && wifiPassword != "")
    {
        WiFi.setAutoReconnect(true);
        WiFi.begin(wifiSSID.c_str(), wifiPassword.c_str());
        debugLog("[WIFI] Connection attempt started (non-blocking)\n");
    }
    else
    {
        debugLog("No WiFi credentials found. Operating in offline mode.\n");
    }

    // Initialize web server/routes at boot so services are ready when WiFi appears later
    handleWebRequests();
    server.begin();

    // Initialize MQTT client configuration regardless of initial WiFi state
    if (mqttEnabled)
    {
        setupMQTT();
    }

    // Initialize weather module regardless of initial WiFi state
    weather.begin();
    weather.setUseFahrenheit(useFahrenheit);
    weather.setSource((WeatherSource)weatherSource);
    weather.setOpenWeatherMapConfig(owmApiKey, owmCity, owmState, owmCountry);
    weather.setHomeAssistantConfig(haUrl, haToken, haEntityId);
    weather.setUpdateInterval(weatherUpdateInterval * 60000); // Convert minutes to milliseconds
    debugLog("Weather module initialized\n");
    debugLog("Weather Source: %d (0=Disabled, 1=OpenWeatherMap, 2=HomeAssistant)\n", weatherSource);
    debugLog("Weather Update Interval: %d minutes\n", weatherUpdateInterval);
    if (weatherSource == 1) {
        debugLog("OpenWeatherMap: City=%s, State=%s, Country=%s, API Key=%s\n",
                     owmCity.c_str(), owmState.c_str(), owmCountry.c_str(),
                     owmApiKey.length() > 0 ? "[SET]" : "[NOT SET]");
    } else if (weatherSource == 2) {
        debugLog("Home Assistant: URL=%s, Entity=%s, Token=%s\n",
                     haUrl.c_str(), haEntityId.c_str(),
                     haToken.length() > 0 ? "[SET]" : "[NOT SET]");
    }

    // Capture initial state so transition logic in loop only fires on real changes
    wifiWasConnected = (WiFi.status() == WL_CONNECTED);
    
    lastInteractionTime = millis();

    // Initialize buttons
    drawButtons();

    // Initialize time from NTP server only if WiFi is connected
    if (wifiWasConnected)
    {
        configTime(0, 0, "pool.ntp.org", "time.nist.gov");
        setenv("TZ", timeZone.c_str(), 1);
        tzset();
        timeSyncInitialized = true;

        // Fetch initial weather data when WiFi is already available at boot
        if (weatherSource != 0) {
            debugLog("Fetching initial weather data...\n");
            bool success = weather.update();
            debugLog("Initial weather fetch: %s\n", success ? "SUCCESS" : "FAILED");
            if (!success) {
                debugLog("Weather error: %s\n", weather.getLastError().c_str());
            }
        }
    }

    // Read initial temperature and humidity
    // Read initial temperature and humidity from AHT20
    // Get initial sensor reading to initialize temperature and humidity values
    float tempReading, humidityReading, pressureReading;
    if (readTemperatureHumidity(tempReading, humidityReading, pressureReading)) {
        float calibratedTemp = getCalibratedTemperature(tempReading);
        float calibratedHumidity = getCalibratedHumidity(humidityReading);
        currentTemp = useFahrenheit ? (calibratedTemp * 9.0 / 5.0 + 32.0) : calibratedTemp;
        currentHumidity = calibratedHumidity;
        
        // Store pressure if BME280 detected
        if (activeSensor == SENSOR_BME280 && !isnan(pressureReading)) {
            currentPressure = pressureReading;
            debugLog("Initial pressure reading: %.1f hPa\n", currentPressure);
        }
        
        debugLog("Initial readings - Temp: %.1f, Humidity: %.1f%%\n", currentTemp, currentHumidity);
    } else {
        debugLog("WARNING: Failed to get initial sensor reading\n");
        // Use fallback values
        currentTemp = 72.0;
        currentHumidity = 50.0;
    }
    
    // Initialize filters with first reading
    filteredTemp = currentTemp;
    filteredHumidity = currentHumidity;
    firstSensorReading = false;

    // Initial display update
    updateDisplay(currentTemp, currentHumidity);

    // Initialize display sleep timing
    lastInteractionTime = millis();

    // Initialize the DS18B20 sensor (GPIO41 USB JTAG already disabled at start of setup)
    debugLog("Initializing DS18B20 sensors on GPIO%d...\n", ONEWIRE_PIN);
    
    // Verify GPIO41 is now high after USB JTAG disable
    int pinStateAfterConfig = gpio_get_level((gpio_num_t)ONEWIRE_PIN);
    debugLog("GPIO%d level after USB JTAG disable: %d (should be 1 with pullup)\n", ONEWIRE_PIN, pinStateAfterConfig);
    
    if (pinStateAfterConfig == 0) {
        debugLog("ERROR: GPIO%d still LOW after USB JTAG disable!\n", ONEWIRE_PIN);
        debugLog("Hardware issue or USB peripheral still active.\n");
    }
    
    // Test OneWire bus by doing a manual reset pulse
    gpio_set_level((gpio_num_t)ONEWIRE_PIN, 0);
    delayMicroseconds(500);
    gpio_set_level((gpio_num_t)ONEWIRE_PIN, 1);
    gpio_set_direction((gpio_num_t)ONEWIRE_PIN, GPIO_MODE_INPUT);  // Release bus for presence pulse
    delayMicroseconds(70);
    int presence = gpio_get_level((gpio_num_t)ONEWIRE_PIN);
    debugLog("OneWire bus reset test: presence = %d (0=device present, 1=no device)\n", presence);
    gpio_set_direction((gpio_num_t)ONEWIRE_PIN, GPIO_MODE_INPUT_OUTPUT_OD);  // Restore open-drain mode
    delay(50);
    
    // NOW create OneWire and DallasTemperature objects AFTER GPIO configuration
    // This is critical - creating them before GPIO41 reconfiguration corrupts their state
    debugLog("Creating OneWire objects AFTER GPIO41 configuration...\n");
    
    oneWire = new OneWire(ONEWIRE_PIN);
    
    // CRITICAL: OneWire's begin() method calls pinMode() which may re-enable USB JTAG!
    // Force GPIO41 back to open-drain mode AFTER OneWire initialization
    debugLog("Re-forcing GPIO41 configuration after OneWire::begin()...\n");
    esp_rom_gpio_pad_select_gpio(ONEWIRE_PIN);
    PIN_FUNC_SELECT(GPIO_PIN_MUX_REG[ONEWIRE_PIN], PIN_FUNC_GPIO);
    gpio_set_direction((gpio_num_t)ONEWIRE_PIN, GPIO_MODE_INPUT_OUTPUT_OD);
    gpio_set_pull_mode((gpio_num_t)ONEWIRE_PIN, GPIO_PULLUP_ONLY);
    gpio_pullup_en((gpio_num_t)ONEWIRE_PIN);
    gpio_set_level((gpio_num_t)ONEWIRE_PIN, 1);
    delay(50);
    
    // Verify GPIO41 is STILL high after OneWire initialization
    int pinStateAfterOneWire = gpio_get_level((gpio_num_t)ONEWIRE_PIN);
    debugLog("GPIO41 level after OneWire init: %d (should be 1)\n", pinStateAfterOneWire);
    
    delay(100);
    
    // Try manual OneWire device search
    debugLog("Performing manual OneWire device search...\n");
    uint8_t addr[8];
    int manualDeviceCount = 0;
    oneWire->reset_search();
    delay(50);
    
    // Try multiple search attempts
    for (int attempt = 0; attempt < 5; attempt++) {
        debugLog("  Search attempt %d...\n", attempt + 1);
        
        // Test reset before each search
        uint8_t resetResult = oneWire->reset();
        debugLog("    Reset result: %d (should be 1 for device present)\n", resetResult);
        if (resetResult == 0) {
            debugLog("    No devices detected on bus (reset failed)\n");
            delay(100);
            continue;
        }
        
        if (oneWire->search(addr)) {
            manualDeviceCount++;
            debugLog("  Device %d ROM: %02X %02X %02X %02X %02X %02X %02X %02X\n",
                     manualDeviceCount, addr[0], addr[1], addr[2], addr[3], addr[4], addr[5], addr[6], addr[7]);
            
            // Verify CRC
            if (OneWire::crc8(addr, 7) != addr[7]) {
                debugLog("    WARNING: CRC invalid!\n");
            } else {
                debugLog("    CRC valid\n");
                
                // Check device family (0x28 = DS18B20)
                if (addr[0] == 0x28) {
                    debugLog("    Device is DS18B20\n");
                    if (manualDeviceCount == 1 && !ds18b20Address1Valid) {
                        memcpy(ds18b20Address1, addr, 8);
                        ds18b20Address1Valid = true;
                    } else if (manualDeviceCount == 2 && !ds18b20Address2Valid) {
                        memcpy(ds18b20Address2, addr, 8);
                        ds18b20Address2Valid = true;
                    }
                } else {
                    debugLog("    Device family code: 0x%02X (not DS18B20)\n", addr[0]);
                }
            }
            delay(10);  // Delay between device discoveries
        } else {
            break;  // No more devices
        }
    }
    debugLog("Manual search found %d device(s)\n", manualDeviceCount);
    
    // Now initialize DallasTemperature library
    ds18b20 = new DallasTemperature(oneWire);
    ds18b20->begin();
    delay(200);  // Wait for DS18B20 sensors to initialize
    
    // Check if DS18B20 sensors are present
    ds18b20->requestTemperatures();
    delay(750);  // Wait for temperature conversion (750ms for 12-bit resolution)
    int ds18b20Count = ds18b20->getDeviceCount();
    debugLog("DS18B20 device count: %d\n", ds18b20Count);
    float tempC = ds18b20->getTempCByIndex(0);
    float returnTempC = ds18b20->getTempCByIndex(1);
    debugLog("DS18B20 readings: Supply=%.1f°C, Return=%.1f°C\n", tempC, returnTempC);
    ds18b20SensorPresent = (ds18b20Count >= 1) && (tempC != DEVICE_DISCONNECTED_C && tempC != -127.0);
    ds18b20ReturnSensorPresent = (ds18b20Count >= 2) && (returnTempC != DEVICE_DISCONNECTED_C && returnTempC != -127.0);
    
    if (ds18b20SensorPresent) {
        debugLog("DS18B20 supply sensor detected\n");
    } else {
        debugLog("DS18B20 supply sensor NOT detected\n");
    }
    if (ds18b20ReturnSensorPresent) {
        debugLog("DS18B20 return sensor detected\n");
    } else {
        debugLog("DS18B20 return sensor NOT detected\n");
    }
    
    // Republish MQTT discovery after DS18B20 initialization
    // (initial discovery happened before sensors were initialized)
    if (mqttEnabled && mqttClient.connected()) {
        debugLog("Republishing Home Assistant discovery with DS18B20 sensors...\n");
        publishHomeAssistantDiscovery();
    }
    
    // Create all mutexes BEFORE spawning any tasks that use them
    displayUpdateMutex = xSemaphoreCreateMutex();
    if (displayUpdateMutex == NULL) {
        debugLog("ERROR: Failed to create display update mutex!\n");
    } else {
        debugLog("Display update mutex created successfully\n");
    }
    
    // Create controlRelays mutex for thread-safe relay control
    controlRelaysMutex = xSemaphoreCreateMutex();
    if (controlRelaysMutex == NULL) {
        debugLog("ERROR: Failed to create controlRelays mutex!\n");
    } else {
        debugLog("Control relays mutex created successfully\n");
    }
    
    // Create radar sensor mutex for thread-safe sensor access
    radarSensorMutex = xSemaphoreCreateMutex();
    if (radarSensorMutex == NULL) {
        debugLog("ERROR: Failed to create radar sensor mutex!\n");
    } else {
        debugLog("Radar sensor mutex created successfully\n");
    }

    // Initialize sensor task watchdog timestamp before spawning the task
    sensorTaskLastAlive = millis();

    // Create sensor task on core 1
    xTaskCreatePinnedToCore(
        sensorTaskFunction,  // Task function
        "SensorTask",       // Name
        10000,             // Stack size
        NULL,              // Parameters
        1,                 // Priority
        &sensorTask,       // Task handle
        1                  // Core 1
    );

    // Option C: Create display update task on core 0
    xTaskCreatePinnedToCore(
        displayUpdateTaskFunction,  // Task function
        "DisplayUpdateTask",       // Name
        4096,                     // Stack size (smaller than sensor task)
        NULL,                     // Parameters
        2,                        // Priority (higher than sensor task)
        &displayUpdateTask,       // Task handle
        0                         // Core 0 (same as main display operations)
    );
    
    debugLog("Dual-core thermostat with centralized display updates setup complete\n");
    debugLog("[BOOT] Setup complete - System ready\n");
    debugLog("[BOOT] Debug console available at /debug\n");
    debugLog("[BOOT] System Version %s\n", sw_version.c_str());
    debugLog("[BOOT] Hostname: %s\n", hostname.c_str());
    
    // Play startup tone to indicate setup is complete
    buzzerStartupTone();

    
}

void loop()
{
    static unsigned long lastWiFiAttemptTime = 0;
    static unsigned long lastMQTTAttemptTime = 0;
    static unsigned long lastDisplayUpdateTime = 0;
    static unsigned long lastSensorReadTime = 0;
    static unsigned long lastFanScheduleTime = 0;
    static unsigned long lastMQTTDataTime = 0;
    static unsigned long lastScheduleCheckTime = 0;
    static unsigned long lastDiagLogTime = 0;
    const unsigned long sensorReadInterval = 2000;    // Read sensors every 2 seconds

    // Check boot button for factory reset
    bool currentBootButtonState = digitalRead(BOOT_BUTTON) == LOW; // Boot button is active LOW
    
    // Detect boot button press
    if (currentBootButtonState && !bootButtonPressed)
    {
        bootButtonPressed = true;
        bootButtonPressStart = millis();
        debugLog("Boot button pressed, holding for factory reset...\n");
    }
    
    // Detect boot button release
    if (!currentBootButtonState && bootButtonPressed)
    {
        bootButtonPressed = false;
        debugLog("Boot button released\n");
    }
    
    // Check if boot button has been held long enough for factory reset
    if (bootButtonPressed && (millis() - bootButtonPressStart > FACTORY_RESET_PRESS_TIME))
    {
        debugLog("Factory reset triggered by boot button!\n");
        
        // Show reset message on display
        tft.fillScreen(COLOR_BACKGROUND);
        tft.setTextColor(COLOR_TEXT, COLOR_BACKGROUND);
        tft.setTextSize(2);
        tft.setCursor(10, 10);
        tft.println("FACTORY RESET");
        tft.setCursor(10, 40);
        tft.println("Restoring defaults...");
        tft.setCursor(10, 70);
        tft.println("Please wait");
        
        // Restore default settings and reboot immediately
        restoreDefaultSettings();
        // ESP.restart() is called in restoreDefaultSettings()
    }

    // Get current time for all timing operations
    unsigned long currentTime = millis();

    // Feed the watchdog timer less frequently for better performance
    static unsigned long lastWatchdogTime = 0;
    if (currentTime - lastWatchdogTime > 1000) {
        esp_task_wdt_reset();
        lastWatchdogTime = currentTime;
    }

    // Sensor task watchdog: if the sensor task hasn't updated in 30s, all relays
    // are forced off to prevent heating/cooling running uncontrolled.
    static unsigned long lastSensorWatchdogLog = 0;
    const unsigned long SENSOR_TASK_TIMEOUT = 30000;
    if (sensorTaskLastAlive > 0 && (currentTime - sensorTaskLastAlive) > SENSOR_TASK_TIMEOUT) {
        digitalWrite(HEAT_RELAY_1_PIN, LOW);
        digitalWrite(HEAT_RELAY_2_PIN, LOW);
        digitalWrite(COOL_RELAY_1_PIN, LOW);
        digitalWrite(COOL_RELAY_2_PIN, LOW);
        digitalWrite(FAN_RELAY_PIN, LOW);
        heatingOn = false;
        coolingOn = false;
        fanOn = false;
        if (currentTime - lastSensorWatchdogLog > 5000) {
            debugLog("[WATCHDOG] Sensor task stalled >30s - all relays forced OFF\n");
            lastSensorWatchdogLog = currentTime;
        }
    }

    // Handle touch input with priority - check this first for responsiveness
    uint16_t x, y;
    static unsigned long lastTouchDebug = 0;
    
    if (tft.getTouch(&x, &y))
    {
        // Debug: Log all touches for diagnosis
        // Ignore touches on the edges of the display (deadzone for case edge artifacts)
        const int TOUCH_DEADZONE = 5;
        const int touchWidth = dispW();
        const int touchHeight = dispH();
        
        unsigned long currentTime = millis();
        if (currentTime - lastTouchDebug > 500) {
            char touchMsg[64];
            snprintf(touchMsg, sizeof(touchMsg), "[TOUCH] X=%u Y=%u DZ=%d\n", x, y, TOUCH_DEADZONE);
            debugLog("%s", touchMsg);
            lastTouchDebug = currentTime;
        }
        
        if (x < TOUCH_DEADZONE || x >= touchWidth - TOUCH_DEADZONE ||
            y < TOUCH_DEADZONE || y >= touchHeight - TOUCH_DEADZONE) {
            // Touch is outside valid area - ignore it (but log it occasionally)
            static unsigned long lastDeadzoneLog = 0;
            if (currentTime - lastDeadzoneLog > 2000) {
                char dzMsg[64];
                snprintf(dzMsg, sizeof(dzMsg), "[FILTERED] X=%u Y=%u (deadzone)\n", x, y);
                debugLog("%s", dzMsg);
                lastDeadzoneLog = currentTime;
            }
        } else {
            // Valid touch within display bounds
            // Wake display if it's asleep
            if (displayIsAsleep) {
                wakeDisplay();
                // Don't process touch input when waking from sleep, just wake up
                // Don't reset interaction time here - wakeDisplay handles it if needed
            } else if (currentTime - lastWakeTime > 500) {
                // Display is awake and we're past the wake debounce period
                // Ignore touches for 500ms after waking to prevent immediate re-sleep
                lastInteractionTime = millis();
                
                // Always handle button presses - removed serial debug for maximum speed
                handleButtonPress(x, y);
                
                // Only handle keyboard touches if we're in WiFi setup mode
                if (inWiFiSetupMode) {
                    handleKeyboardTouch(x, y, isUpperCaseKeyboard);
                }
            }
        }
    }


    // If in WiFi setup mode, skip the normal display updates and sensor readings
    if (inWiFiSetupMode) {
        // Only minimal processing in WiFi setup mode - no delays for maximum touch responsiveness
        return;
    }

    // If in Settings UI, pause normal loop to keep touch responsive
    if (inSettingsMenu) {
        settingsLoopTick();
        return;
    }

    // The rest of the loop function only runs when NOT in WiFi/setup/settings modes
    // Sensor reading now handled by background task on core 1

    // Control fan based on schedule - only check every 30 seconds
    if (currentTime - lastFanScheduleTime > 30000) {
        controlFanSchedule();
        lastFanScheduleTime = currentTime;
    }

    // Check temperature schedule - only check every 60 seconds
    if (currentTime - lastScheduleCheckTime > 60000) {
        checkSchedule();
        lastScheduleCheckTime = currentTime;
    }
    
    // Update weather data if enabled and connected to WiFi
    static unsigned long lastWeatherDebug = 0;
    if (weatherSource != 0 && WiFi.status() == WL_CONNECTED) {
        bool updated = weather.update(); // Will only update if interval has passed
        
        // Debug weather status every 60 seconds
        if (millis() - lastWeatherDebug > 60000) {
            debugLog("WEATHER: Source=%d, Valid=%d, Temp=%.1f, Condition=%s, Error=%s\n",
                         weatherSource,
                         weather.isDataValid(),
                         weather.getData().temperature,
                         weather.getData().condition.c_str(),
                         weather.getLastError().c_str());
            lastWeatherDebug = millis();
        }
    }

    // Update display brightness based on light sensor - check every 1 second
    updateDisplayBrightness();

    // Check motion sensor every 100ms
    static unsigned long lastMotionCheck = 0;
    if (millis() - lastMotionCheck > 100) {
        lastMotionCheck = millis();
        readMotionSensor();
    }

    // Debug LD2410 status every 30 seconds
    static unsigned long lastLD2410Status = 0;
    if (millis() - lastLD2410Status > 30000) {
        lastLD2410Status = millis();
        if (ld2410Connected) {
            debugLog("LD2410: Status - Connected: %s, Motion: %s, Last motion: %lu ms ago\\n",
                          ld2410Connected ? "YES" : "NO",
                          motionDetected ? "ACTIVE" : "INACTIVE",
                          millis() - lastMotionTime);
        } else {
            debugLog("LD2410: Status - Sensor not detected, display control via touch only\n");
        }
    }

    // Check if display should go to sleep due to inactivity
    checkDisplaySleep();
    
    // Periodic debug output to buffer every 5 seconds
    static unsigned long lastDebugOutput = 0;
    if (currentTime - lastDebugOutput > 5000) {
        lastDebugOutput = currentTime;
        debugLog("[DEBUG] Temp=%.1f H=%.1f Sleep=%d SleepTime=%lu\n",
                 currentTemp, currentHumidity, displayIsAsleep,
                 currentTime - lastInteractionTime);
    }
    // Periodic display updates - now called from main loop for thread safety with TFT library
    if (currentTime - lastDisplayUpdateTime > displayUpdateInterval)
    {
        updateDisplay(currentTemp, currentHumidity);
        lastDisplayUpdateTime = currentTime;
    }

    // Attempt to connect to WiFi if not connected - check every 30 seconds
    if (WiFi.status() != WL_CONNECTED && currentTime - lastWiFiAttemptTime > 30000)
    {
        connectToWiFi();
        lastWiFiAttemptTime = currentTime;
    }

    // Handle WiFi connect/disconnect transitions without blocking UI responsiveness
    handleWiFiConnectionState(currentTime);
    
    if (mqttEnabled)
    {
        // Attempt to reconnect to MQTT if not connected and WiFi is connected - check every 15 seconds
        if (WiFi.status() == WL_CONNECTED && !mqttClient.connected() && currentTime - lastMQTTAttemptTime > 15000)
        {
            reconnectMQTT();
            lastMQTTAttemptTime = currentTime;
        }
        mqttClient.loop();
        
        // Send MQTT feedback immediately if settings changed via MQTT
        if (mqttFeedbackNeeded && mqttClient.connected()) {
            debugLog("[MQTT] Sending immediate feedback for settings change\n");
            sendMQTTData();
            mqttFeedbackNeeded = false;
            lastMQTTDataTime = currentTime;
        }
        
        // Send MQTT data only every 10 seconds instead of every loop
        if (currentTime - lastMQTTDataTime > 10000) {
            sendMQTTData();
            lastMQTTDataTime = currentTime;
        }
    }
    else
    {
        if (mqttClient.connected())
        {
            mqttClient.disconnect();
        }
    }

    // Control relays more frequently for immediate response to setting changes
    static unsigned long lastRelayControlTime = 0;
    if (currentTime - lastRelayControlTime > 1000) { // Control relays every 1 second
        controlRelays(currentTemp);
        lastRelayControlTime = currentTime;
    }

    // Periodic diagnostics: heap and stack watermarks
    if (currentTime - lastDiagLogTime > 30000) { // every 30 seconds
        logRuntimeDiagnostics();
        lastDiagLogTime = currentTime;
    }

    // LEDs are updated from state-changing functions (activateHeating, activateCooling, turnOffAllRelays)
    // No need for frequent polling - only update when state actually changes
}

void logRuntimeDiagnostics() {
    size_t free8 = heap_caps_get_free_size(MALLOC_CAP_8BIT);
    size_t largest8 = heap_caps_get_largest_free_block(MALLOC_CAP_8BIT);
    size_t minFree8 = heap_caps_get_minimum_free_size(MALLOC_CAP_8BIT);

    UBaseType_t mainWatermark = uxTaskGetStackHighWaterMark(NULL);
    UBaseType_t sensorWatermark = sensorTask ? uxTaskGetStackHighWaterMark(sensorTask) : 0;
    UBaseType_t displayWatermark = displayUpdateTask ? uxTaskGetStackHighWaterMark(displayUpdateTask) : 0;

    debugLog("[DIAG] Heap: free=%uB, largest=%uB, min_free=%uB\n",
                  (unsigned)free8, (unsigned)largest8, (unsigned)minFree8);
    debugLog("[DIAG] Stack HWM (words): main=%lu, sensor=%lu, display=%lu\n",
                  (unsigned long)mainWatermark,
                  (unsigned long)sensorWatermark,
                  (unsigned long)displayWatermark);
}

void setupWiFi()
{
    // hostname already loaded by loadSettings() - don't override it with wrong key
    WiFi.setHostname(hostname.c_str()); // Set the WiFi device name

    wifiSSID = preferences.getString("wifiSSID", "");
    wifiPassword = preferences.getString("wifiPassword", "");

    if (wifiSSID != "" && wifiPassword != "")
    {
        WiFi.begin(wifiSSID.c_str(), wifiPassword.c_str());
        unsigned long startAttemptTime = millis();

        // Only try to connect for 10 seconds
        while (WiFi.status() != WL_CONNECTED && millis() - startAttemptTime < 10000)
        {
            delay(1000);
            debugLog("Connecting to WiFi...\n");
        }

        if (WiFi.status() == WL_CONNECTED)
        {
            debugLog("Connected to WiFi\n");
            debugLog("IP Address: %s\n", WiFi.localIP().toString().c_str());
        }
        else
        {
            debugLog("Failed to connect to WiFi\n");
            enterWiFiCredentials();
        }
    }
    else
    {
        // No WiFi credentials found, prompt user to enter them via touch screen
        debugLog("No WiFi credentials found. Please enter them via the touch screen.\n");
        enterWiFiCredentials();
    }
}

void connectToWiFi()
{
    if (wifiSSID != "" && wifiPassword != "")
    {
        wl_status_t status = WiFi.status();
        if (status == WL_CONNECTED) {
            return;
        }

        // If a previous begin() is still in progress, avoid restarting it.
        if (status == WL_IDLE_STATUS) {
            debugLog("[WIFI] Connection already in progress\n");
            return;
        }

        debugLog("[WIFI] Starting reconnect attempt for SSID: %s\n", wifiSSID.c_str());
        WiFi.begin(wifiSSID.c_str(), wifiPassword.c_str());
    }
    else
    {
        // Having no credentials is fine - don't trigger WiFi setup automatically
        debugLog("No WiFi credentials found. Device operating in offline mode.\n");
        // Note: User can press the WiFi button on the display to configure WiFi if desired
    }
}

void handleWiFiConnectionState(unsigned long currentTime)
{
    bool wifiNowConnected = (WiFi.status() == WL_CONNECTED);

    if (wifiNowConnected && !wifiWasConnected)
    {
        debugLog("[WIFI] Connected. IP Address: %s\n", WiFi.localIP().toString().c_str());

        if (!timeSyncInitialized) {
            configTime(0, 0, "pool.ntp.org", "time.nist.gov");
            setenv("TZ", timeZone.c_str(), 1);
            tzset();
            timeSyncInitialized = true;
            debugLog("[WIFI] NTP time sync initialized\n");
        }

        if (mqttEnabled && !mqttClient.connected()) {
            reconnectMQTT();
        }

        // Trigger a weather refresh once after reconnection.
        if (weatherSource != 0) {
            bool success = weather.update();
            debugLog("[WEATHER] Refresh after WiFi reconnect: %s\n", success ? "SUCCESS" : "FAILED");
        }
    }
    else if (!wifiNowConnected && wifiWasConnected)
    {
        debugLog("[WIFI] Disconnected\n");
    }

    // Periodic heartbeat while disconnected (every 60s) helps diagnose field issues.
    static unsigned long lastDisconnectedLog = 0;
    if (!wifiNowConnected && currentTime - lastDisconnectedLog > 60000) {
        lastDisconnectedLog = currentTime;
        debugLog("[WIFI] Offline, awaiting reconnect\n");
    }

    wifiWasConnected = wifiNowConnected;
}

void enterWiFiCredentials()
{
    // Make sure we clear the screen completely before drawing the keyboard
    tft.fillScreen(COLOR_BACKGROUND);
    
    // Reset input text and set initial state to entering SSID
    inputText = "";
    isEnteringSSID = true;
    
    // Draw the keyboard with the screen freshly cleared
    drawKeyboard(isUpperCaseKeyboard);

    // Prevent an indefinite lock if credentials flow is entered while WiFi is unavailable.
    const unsigned long credentialsWaitTimeoutMs = 120000;
    unsigned long credentialsWaitStart = millis();
    
    while (WiFi.status() != WL_CONNECTED)
    {
        uint16_t x, y;
        if (tft.getTouch(&x, &y))
        {
            handleKeyboardTouch(x, y, isUpperCaseKeyboard);
        }
        delay(100); // Reduced delay for more responsive touch handling
        
        // Periodically print status message
        static unsigned long lastStatusPrint = 0;
        unsigned long currentTime = millis();
        if (currentTime - lastStatusPrint > 5000) {
            debugLog("Waiting for WiFi credentials...\n");
            lastStatusPrint = currentTime;
        }

        if (currentTime - credentialsWaitStart > credentialsWaitTimeoutMs) {
            debugLog("[WIFI] Credential entry timeout; returning to main UI\n");
            tft.fillScreen(COLOR_BACKGROUND);
            tft.setTextColor(COLOR_WARNING, COLOR_BACKGROUND);
            tft.setTextSize(2);
            tft.setCursor(20, 100);
            tft.println("WiFi setup timeout");
            tft.setTextColor(COLOR_TEXT, COLOR_BACKGROUND);
            tft.setCursor(20, 130);
            tft.println("Returning to main...");
            delay(1200);
            return;
        }
    }
}

void drawKeyboard(bool isUpperCaseKeyboard)
{
    const int keyW = uiScaleX(KEY_WIDTH);
    const int keyH = uiScaleY(KEY_HEIGHT);
    const int keySpacingX = uiScaleX(KEY_SPACING);
    const int keySpacingY = uiScaleY(KEY_SPACING);
    const int keyOffsetX = uiScaleX(KEYBOARD_X_OFFSET);
    const int keyOffsetY = uiScaleY(KEYBOARD_Y_OFFSET);

    // Clear the entire screen first to prevent any overlapping elements
    tft.fillScreen(COLOR_BACKGROUND);
    
    // Draw header with better styling
    tft.setTextColor(COLOR_TEXT, COLOR_BACKGROUND);
    tft.setTextSize(2);
    tft.setCursor(uiScaleX(10), uiScaleY(10));
    const char* header = "Enter SSID:";
    if (keyboardMode == KB_WIFI_PASS) {
        header = "Enter Password:";
    } else if (keyboardMode == KB_HOSTNAME) {
        header = "Enter Hostname:";
    }
    tft.println(header);

    // Back button to exit to main/settings
    int backX = uiScaleX(250), backY = uiScaleY(5), backW = uiScaleX(60), backH = uiScaleY(25);
    tft.fillRect(backX, backY, backW, backH, COLOR_WARNING);
    tft.drawRect(backX, backY, backW, backH, COLOR_TEXT);
    tft.setTextColor(TFT_BLACK, COLOR_WARNING);
    tft.setTextSize(1);
    tft.setCursor(backX + uiScaleX(10), backY + uiScaleY(9));
    tft.print("Back");
    tft.setTextColor(COLOR_TEXT, COLOR_BACKGROUND);
    tft.setTextSize(2);
    
    // Draw input text area with border
    tft.drawRect(uiScaleX(5), uiScaleY(35), uiScaleX(310), uiScaleY(30), COLOR_TEXT);
    tft.fillRect(uiScaleX(6), uiScaleY(36), uiScaleX(308), uiScaleY(28), COLOR_BACKGROUND);
    tft.setTextColor(COLOR_TEXT, COLOR_BACKGROUND);
    tft.setTextSize(2);
    tft.setCursor(uiScaleX(10), uiScaleY(42));
    tft.println(inputText);

    // Select keyboard layout
    const char* (*keys)[10] = isUpperCaseKeyboard ? KEYBOARD_UPPER : KEYBOARD_LOWER;

    // Draw keyboard with improved styling
    tft.setTextSize(1);
    for (int row = 0; row < 5; row++)
    {
        for (int col = 0; col < 10; col++)
        {
            int x = col * (keyW + keySpacingX) + keyOffsetX;
            int y = row * (keyH + keySpacingY) + keyOffsetY;
            
            // Choose key color based on function
            uint16_t keyColor = COLOR_SECONDARY;
            uint16_t textColor = TFT_BLACK;
            
            const char* keyLabel = keys[row][col];
            if (strcmp(keyLabel, "DEL") == 0 || strcmp(keyLabel, "CLR") == 0) {
                keyColor = COLOR_WARNING;
            } else if (strcmp(keyLabel, "OK") == 0) {
                keyColor = COLOR_SUCCESS;
            } else if (strcmp(keyLabel, "SHIFT") == 0) {
                keyColor = isUpperCaseKeyboard ? COLOR_PRIMARY : COLOR_ACCENT;
            } else if (strcmp(keyLabel, "SPC") == 0) {
                keyColor = COLOR_PRIMARY;
            }
            
            // Draw key background
            tft.fillRect(x, y, keyW, keyH, keyColor);
            tft.drawRect(x, y, keyW, keyH, COLOR_TEXT);
            
            // Draw key label - center the text
            tft.setTextColor(textColor);
            int textWidth = strlen(keyLabel) * 6; // Approximate width
            int textX = x + (keyW - textWidth) / 2;
            int textY = y + (keyH - 8) / 2;
            tft.setCursor(textX, textY);
            
            // Special display for space key
            if (strcmp(keyLabel, "SPC") == 0) {
                tft.print("SPACE");
            } else {
                tft.print(keyLabel);
            }
        }
    }
}

void handleKeyPress(int row, int col)
{
    const int keyW = uiScaleX(KEY_WIDTH);
    const int keyH = uiScaleY(KEY_HEIGHT);
    const int keySpacingX = uiScaleX(KEY_SPACING);
    const int keySpacingY = uiScaleY(KEY_SPACING);
    const int keyOffsetX = uiScaleX(KEYBOARD_X_OFFSET);
    const int keyOffsetY = uiScaleY(KEYBOARD_Y_OFFSET);

    // Get the appropriate keyboard layout
    const char* (*keys)[10] = isUpperCaseKeyboard ? KEYBOARD_UPPER : KEYBOARD_LOWER;
    const char* keyLabel = keys[row][col];

    // Provide visual feedback for key press
    int x = col * (keyW + keySpacingX) + keyOffsetX;
    int y = row * (keyH + keySpacingY) + keyOffsetY;
    
    // Flash the key white briefly for feedback
    tft.fillRect(x, y, keyW, keyH, TFT_WHITE);
    tft.drawRect(x, y, keyW, keyH, COLOR_TEXT);
    tft.setTextColor(TFT_BLACK);
    int textWidth = strlen(keyLabel) * 6;
    int textX = x + (keyW - textWidth) / 2;
    int textY = y + (keyH - 8) / 2;
    tft.setCursor(textX, textY);
    tft.setTextSize(1);
    if (strcmp(keyLabel, "SPC") == 0) {
        tft.print("SPACE");
    } else {
        tft.print(keyLabel);
    }
    delay(100); // Brief visual feedback

    // Handle key functionality
    if (strcmp(keyLabel, "DEL") == 0)
    {
        if (inputText.length() > 0)
        {
            inputText.remove(inputText.length() - 1);
        }
    }
    else if (strcmp(keyLabel, "SPC") == 0)
    {
        if (inputText.length() < 30) { // Limit input length
            inputText += " ";
        }
    }
    else if (strcmp(keyLabel, "CLR") == 0)
    {
        inputText = "";
    }
    else if (strcmp(keyLabel, "OK") == 0)
    {
        // Context-aware OK handling: WiFi SSID/Pass or Hostname
        if (keyboardMode == 2) { // KB_HOSTNAME
            if (inputText.length() > 0) {
                hostname = inputText;
                saveSettings();
                exitKeyboardToPreviousScreen();
                return;
            }
        } else if (isEnteringSSID) {
            if (inputText.length() > 0) {
                wifiSSID = inputText;
                inputText = "";
                isEnteringSSID = false;
                keyboardMode = (KeyboardMode)1; // KB_WIFI_PASS
                drawKeyboard(isUpperCaseKeyboard);
                return; // Early return to avoid input update
            }
        }
        else
        {
            if (inputText.length() > 0) {
                wifiPassword = inputText;
                
                // Show connection attempt message
                tft.fillScreen(COLOR_BACKGROUND);
                tft.setTextColor(COLOR_TEXT, COLOR_BACKGROUND);
                tft.setTextSize(2);
                tft.setCursor(50, 100);
                tft.println("Connecting...");
                tft.setCursor(30, 130);
                tft.println("Please wait");
                
                saveWiFiSettings();
                WiFi.begin(wifiSSID.c_str(), wifiPassword.c_str());
                unsigned long startAttemptTime = millis();

                // Try to connect for 10 seconds with progress indicator
                int dots = 0;
                while (WiFi.status() != WL_CONNECTED && millis() - startAttemptTime < 10000)
                {
                    delay(500);
                    tft.setCursor(30 + (dots * 12), 160);
                    tft.print(".");
                    dots = (dots + 1) % 20;
                    debugLog("Connecting to WiFi...\n");
                }

                if (WiFi.status() == WL_CONNECTED)
                {
                    tft.fillScreen(COLOR_BACKGROUND);
                    tft.setCursor(50, 100);
                    tft.setTextColor(COLOR_SUCCESS, COLOR_BACKGROUND);
                    tft.println("Connected!");
                    tft.setTextColor(COLOR_TEXT, COLOR_BACKGROUND);
                    tft.setCursor(30, 130);
                    tft.println("Restarting...");
                    debugLog("Connected to WiFi\n");
                    debugLog("IP Address: %s\n", WiFi.localIP().toString().c_str());
                    delay(2000);
                    ESP.restart();
                }
                else
                {
                    tft.fillScreen(COLOR_BACKGROUND);
                    tft.setCursor(30, 100);
                    tft.setTextColor(COLOR_WARNING, COLOR_BACKGROUND);
                    tft.println("Failed to connect");
                    tft.setTextColor(COLOR_TEXT, COLOR_BACKGROUND);
                    tft.setCursor(30, 130);
                    tft.println("Touch to retry");
                    debugLog("Failed to connect to WiFi\n");
                    delay(3000);
                    // Reset and return to keyboard
                    inputText = "";
                    isEnteringSSID = true;
                    drawKeyboard(isUpperCaseKeyboard);
                    return;
                }
            }
        }
    }
    else if (strcmp(keyLabel, "SHIFT") == 0)
    {
        isUpperCaseKeyboard = !isUpperCaseKeyboard;
        drawKeyboard(isUpperCaseKeyboard);
        return; // Early return to avoid input update
    }
    else
    {
        // Add regular character if within length limit
        if (inputText.length() < 30) {
            inputText += keyLabel;
        }
    }

    // Update input display
    tft.fillRect(uiScaleX(6), uiScaleY(36), uiScaleX(308), uiScaleY(28), COLOR_BACKGROUND);
    tft.setTextColor(COLOR_TEXT, COLOR_BACKGROUND);
    tft.setTextSize(2);
    tft.setCursor(uiScaleX(10), uiScaleY(42));
    tft.println(inputText);
    
    // Redraw the keyboard to restore normal key colors
    drawKeyboard(isUpperCaseKeyboard);
}

void drawButtons()
{
    // Draw the "+" button
    tft.fillRect(uiScaleX(270), uiScaleY(200), uiScaleX(40), uiScaleY(40), COLOR_SUCCESS);
    tft.setCursor(uiScaleX(285), uiScaleY(215));
    tft.setTextColor(TFT_BLACK);
    tft.setTextSize(2);
    tft.print("+");

    // Move the "-" button to the far bottom left corner
    tft.fillRect(uiScaleX(0), uiScaleY(200), uiScaleX(40), uiScaleY(40), COLOR_WARNING);
    tft.setCursor(uiScaleX(15), uiScaleY(215));
    tft.setTextColor(TFT_BLACK);
    tft.setTextSize(2);
    tft.print("-");

    // Draw the Settings button between minus and mode buttons
    tft.fillRect(uiScaleX(47), uiScaleY(200), uiScaleX(68), uiScaleY(40), COLOR_SECONDARY);
    tft.setTextColor(TFT_BLACK);
    tft.setTextSize(1);
    // Center "Settings" text on button (button center x=81, text width ~42px at size 1)
    tft.setCursor(uiScaleX(57), uiScaleY(214));
    tft.print("Settings");

    // Draw the thermostat mode button
    tft.fillRect(uiScaleX(125), uiScaleY(200), uiScaleX(60), uiScaleY(40), COLOR_PRIMARY);
    tft.setCursor(uiScaleX(130), uiScaleY(208));
    tft.setTextColor(TFT_BLACK);
    tft.setTextSize(1);
    tft.print("Mode:");
    tft.setCursor(uiScaleX(133), uiScaleY(220));
    tft.setTextSize(2);
    tft.print(thermostatMode);

    // Draw the fan mode button - make it wider to fit "cycle"
    tft.fillRect(uiScaleX(195), uiScaleY(200), uiScaleX(65), uiScaleY(40), COLOR_ACCENT);
    
    tft.setCursor(uiScaleX(205), uiScaleY(208));
    tft.setTextColor(TFT_BLACK);
    tft.setTextSize(1);
    tft.print("Fan:");
    
    // Adjust text position based on fan mode to center it
    int fanTextX = 210;
    if (fanMode == "on") {
        fanTextX = 215;
    } else if (fanMode == "auto") {
        fanTextX = 205;
    } else if (fanMode == "cycle") {
        fanTextX = 200;
    }
    
    tft.setCursor(uiScaleX(fanTextX), uiScaleY(220));
    tft.setTextColor(TFT_BLACK);
    tft.setTextSize(2);
    tft.print(fanMode);


}

void handleButtonPress(uint16_t x, uint16_t y)
{
    // Convert physical touch coordinates to 320x240 virtual UI space.
    x = uiUnscaleX(x);
    y = uiUnscaleY(y);

    // Provide immediate audio feedback for touch
    buzzerBeep(50);
    
    unsigned long startTime = millis();
    
    // Add touch debounce mechanism to prevent accidental double touches
    static unsigned long lastButtonPressTime = 0;
    unsigned long currentTime = millis();
    
    // If less than 300ms has passed since the last button press, ignore this touch
    // This prevents rapid mode switching that can cause relay logic delays
    if (currentTime - lastButtonPressTime < 300) {
        return;
    }
    
    lastButtonPressTime = currentTime;
    
    // If keyboard is active, ignore main button handling (keyboard/back handles its own touches)
    if (inWiFiSetupMode) {
        return;
    }
    
    // Route touches to settings UI when active
    if (inSettingsMenu) {
        if (settingsHandleTouch(x, y)) {
            return;
        }
        // If not consumed, ignore to avoid falling through to main controls
        return;
    }
    
    // Shower mode toggle - touch the set temp area (center display)
    debugLog("[DEBUG] Touch: x=%d, y=%d, showerModeEnabled=%d\n", x, y, showerModeEnabled);
    if (showerModeEnabled && x > 60 && x < 260 && y > 100 && y < 140) {
        showerModeActive = !showerModeActive;
        if (showerModeActive) {
            showerModeStartTime = millis();
            debugLog("[SHOWER MODE] Activated - duration %d minutes\n", showerModeDuration);
        } else {
            debugLog("[SHOWER MODE] Deactivated\n");
        }
        updateDisplay(currentTemp, currentHumidity);
        sendMQTTData();
        return;
    }
    
    // Settings button (formerly WiFi) to open settings menu
    if (x > 45 && x < 125 && y > 195 && y < 245) // Settings button area
    {
        enterSettingsMenu();
        return;
    }
    
    // Increase the touchable area slightly to make buttons easier to hit
    
    // "+" button
    if (x > 265 && x < 315 && y > 195 && y < 245)
    {
        if (!showSetTempOnMainDisplay || millis() >= showSetTempUntil) {
            showSetTempOnMainDisplay = true;
            showSetTempUntil = millis() + SETPOINT_DISPLAY_TIMEOUT_MS;
            updateDisplay(currentTemp, currentHumidity);
            return;
        }

        showSetTempUntil = millis() + SETPOINT_DISPLAY_TIMEOUT_MS;

        // Enable and persist schedule override when manually adjusting temperature while schedule is active
        if (scheduleEnabled && !scheduleOverride) {
            scheduleOverride = true;
            overrideEndTime = millis() + (scheduleOverrideDuration * 60000UL);
            debugLog("SCHEDULE: Override enabled due to manual temperature adjustment\n");
        }
        
        if (thermostatMode == "heat")
        {
            setTempHeat += 0.5;
            if (setTempHeat > 95) setTempHeat = 95;
            if (setTempHeat < 50) setTempHeat = 50;
            if (thermostatMode == "auto" && setTempCool - setTempHeat < tempDifferential)
            {
                setTempCool = setTempHeat + tempDifferential;
                if (!handlingMQTTMessage) mqttClient.publish("thermostat/setTempCool", String(setTempCool).c_str(), true);
            }
            if (!handlingMQTTMessage) mqttClient.publish("thermostat/setTempHeat", String(setTempHeat).c_str(), true);
        }
        else if (thermostatMode == "cool")
        {
            setTempCool += 0.5;
            if (setTempCool > 95) setTempCool = 95;
            if (setTempCool < 50) setTempCool = 50;
            if (thermostatMode == "auto" && setTempCool - setTempHeat < tempDifferential)
            {
                setTempHeat = setTempCool - tempDifferential;
                if (!handlingMQTTMessage) mqttClient.publish("thermostat/setTempHeat", String(setTempHeat).c_str(), true);
            }
            if (!handlingMQTTMessage) mqttClient.publish("thermostat/setTempCool", String(setTempCool).c_str(), true);
        }
        else if (thermostatMode == "auto")
        {
            setTempAuto += 0.5;
            if (setTempAuto > 95) setTempAuto = 95;
            if (setTempAuto < 50) setTempAuto = 50;
            if (!handlingMQTTMessage) mqttClient.publish("thermostat/setTempAuto", String(setTempAuto).c_str(), true);
        }
        // Single atomic save of all settings (including schedule override if set above)
        saveSettings();
        sendMQTTData();
        // Update display immediately for better responsiveness
        updateDisplay(currentTemp, currentHumidity);
    }
    else if (x > 0 && x < 45 && y > 195 && y < 245) // "-" button with slightly increased touch area
    {
        if (!showSetTempOnMainDisplay || millis() >= showSetTempUntil) {
            showSetTempOnMainDisplay = true;
            showSetTempUntil = millis() + SETPOINT_DISPLAY_TIMEOUT_MS;
            updateDisplay(currentTemp, currentHumidity);
            return;
        }

        showSetTempUntil = millis() + SETPOINT_DISPLAY_TIMEOUT_MS;

        // Enable and persist schedule override when manually adjusting temperature while schedule is active
        if (scheduleEnabled && !scheduleOverride) {
            scheduleOverride = true;
            overrideEndTime = millis() + (scheduleOverrideDuration * 60000UL);
            debugLog("SCHEDULE: Override enabled due to manual temperature adjustment\n");
        }
        
        if (thermostatMode == "heat")
        {
            setTempHeat -= 0.5;
            if (setTempHeat > 95) setTempHeat = 95;
            if (setTempHeat < 50) setTempHeat = 50;
            if (thermostatMode == "auto" && setTempCool - setTempHeat < tempDifferential)
            {
                setTempCool = setTempHeat + tempDifferential;
                if (!handlingMQTTMessage) mqttClient.publish("thermostat/setTempCool", String(setTempCool).c_str(), true);
            }
            if (!handlingMQTTMessage) mqttClient.publish("thermostat/setTempHeat", String(setTempHeat).c_str(), true);
        }
        else if (thermostatMode == "cool")
        {
            setTempCool -= 0.5;
            if (setTempCool > 95) setTempCool = 95;
            if (setTempCool < 50) setTempCool = 50;
            if (thermostatMode == "auto" && setTempCool - setTempHeat < tempDifferential)
            {
                setTempHeat = setTempCool - tempDifferential;
                if (!handlingMQTTMessage) mqttClient.publish("thermostat/setTempHeat", String(setTempHeat).c_str(), true);
            }
            if (!handlingMQTTMessage) mqttClient.publish("thermostat/setTempCool", String(setTempCool).c_str(), true);
        }
        else if (thermostatMode == "auto")
        {
            setTempAuto -= 0.5;
            if (setTempAuto > 95) setTempAuto = 95;
            if (setTempAuto < 50) setTempAuto = 50;
            if (!handlingMQTTMessage) mqttClient.publish("thermostat/setTempAuto", String(setTempAuto).c_str(), true);
        }
        // Single atomic save of all settings (including schedule override if set above)
        saveSettings();
        sendMQTTData();
        // Update display immediately for better responsiveness
        updateDisplay(currentTemp, currentHumidity);
    }
    else if (x > 125 && x < 195 && y > 195 && y < 245) // Mode button with slightly increased touch area
    {
        String oldMode = thermostatMode;
        String newMode = "auto"; // Default next mode
        
        // Determine next mode
        if (thermostatMode == "auto")
            newMode = "heat";
        else if (thermostatMode == "heat")
            newMode = "cool";
        else if (thermostatMode == "cool")
            newMode = "off";
        else
            newMode = "auto";
        
        // Check mode switch delay: allow immediate switch to OFF, delay others
        unsigned long currentTime = millis();
        bool isSwitchingToOff = (newMode == "off");
        bool delayElapsed = (currentTime - lastModeSwitchTime >= MODE_SWITCH_DELAY_MS);
        
        if (isSwitchingToOff || delayElapsed) {
            thermostatMode = newMode;
            lastModeSwitchTime = currentTime;
            debugLog("[DEBUG] Mode switched: %s -> %s (delay_ok=%d)\n", oldMode.c_str(), thermostatMode.c_str(), (isSwitchingToOff || delayElapsed));
            
            saveSettings();
            sendMQTTData();
            // Immediately update relays to reflect mode change
            controlRelays(currentTemp);
            // Update display after relays for accurate indicators
            updateDisplay(currentTemp, currentHumidity);
            setDisplayUpdateFlag(); // Option C: Request display update
        } else {
            debugLog("[DEBUG] Mode switch blocked: %s (too soon, need to wait %lu ms)\n", newMode.c_str(), MODE_SWITCH_DELAY_MS - (currentTime - lastModeSwitchTime));
        }
    }
    else if (x > 195 && x < 265 && y > 195 && y < 245) // Fan button with slightly increased touch area
    {
        // Change fan mode
        String oldMode = fanMode;
        if (fanMode == "auto")
            fanMode = "on";
        else if (fanMode == "on")
            fanMode = "cycle";
        else
            fanMode = "auto";

        debugLog("[FAN] Fan mode changed: %s -> %s\n", oldMode.c_str(), fanMode.c_str());
        saveSettings();
        sendMQTTData();
        // Immediately update relays to reflect fan mode change
        controlRelays(currentTemp);
        // Update display after relays for accurate indicators
        updateDisplay(currentTemp, currentHumidity);
    }
}

void setupMQTT()
{
    // Keep network outages from stalling the main loop on socket operations.
    espClient.setTimeout(3000);
    mqttClient.setServer(mqttServer.c_str(), mqttPort);
    mqttClient.setBufferSize(1024); // Ensure buffer size is sufficient for large payloads
    mqttClient.setCallback(mqttCallback);
}

void reconnectMQTT()
{
    // Non-blocking approach - only try once per function call
    if (!mqttClient.connected())
    {
        debugLog("Attempting MQTT connection to server: %s port: %d username: %s\n",
             mqttServer.c_str(), mqttPort, mqttUsername.c_str());
        
        if (mqttClient.connect(hostname.c_str(), mqttUsername.c_str(), mqttPassword.c_str())) {
            debugLog(" - Connected successfully\n");

            // Subscribe to necessary topics
            String tempSetTopic = hostname + "/target_temperature/set";
            String modeSetTopic = hostname + "/mode/set";
            String fanModeSetTopic = hostname + "/fan_mode/set";
            String showerModeSetTopic = hostname + "/shower_mode/set";
            String scheduleEnabledSetTopic = hostname + "/schedule_enabled/set";
            String scheduleOverrideSetTopic = hostname + "/schedule_override/set";
            String scheduleSetTopic = hostname + "/schedule/set";
            mqttClient.subscribe(tempSetTopic.c_str());
            mqttClient.subscribe(modeSetTopic.c_str());
            mqttClient.subscribe(fanModeSetTopic.c_str());
            mqttClient.subscribe(showerModeSetTopic.c_str());
            mqttClient.subscribe(scheduleEnabledSetTopic.c_str());
            mqttClient.subscribe(scheduleOverrideSetTopic.c_str());
            mqttClient.subscribe(scheduleSetTopic.c_str());

            // Publish Home Assistant discovery messages
            publishHomeAssistantDiscovery();
            
            // Reset MQTT data cache so all values get republished
            resetMQTTDataCache();
            
            // Immediately publish current state so Home Assistant doesn't show "unknown"
            sendMQTTData();
        }
        else
        {
            int mqttState = mqttClient.state();
            debugLog(" - Connection failed, rc=%d (", mqttState);
            
            // Provide human-readable error messages
            switch(mqttState) {
                case -4: debugLog("MQTT_CONNECTION_TIMEOUT"); break;
                case -3: debugLog("MQTT_CONNECTION_LOST"); break;
                case -2: debugLog("MQTT_CONNECT_FAILED"); break;
                case -1: debugLog("MQTT_DISCONNECTED"); break;
                case 1: debugLog("MQTT_CONNECT_BAD_PROTOCOL"); break;
                case 2: debugLog("MQTT_CONNECT_BAD_CLIENT_ID"); break;
                case 3: debugLog("MQTT_CONNECT_UNAVAILABLE"); break;
                case 4: debugLog("MQTT_CONNECT_BAD_CREDENTIALS"); break;
                case 5: debugLog("MQTT_CONNECT_UNAUTHORIZED"); break;
                default: debugLog("UNKNOWN ERROR"); break;
            }
            
            debugLog(")\n");
            debugLog("Server: %s, Port: %d\n", mqttServer.c_str(), mqttPort);
        }
    }
}
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
