jrtaylor71/ESP32-DevKitC3-Simple-Thermostat-PCB/include/SettingsUI.h

/*
 * SettingsUI - On-screen settings menu for ESP32-S3 Simple Thermostat
 * Copyright (c) 2025 Jonn Taylor
 * 
 * Provides TFT-based settings menu for:
 * - WiFi configuration
 * - Comfort settings (temp swing, auto swing, fan relay, units)
 * - HVAC advanced (stage2 enable, runtime, delta)
 * - Hostname
 * 
 * Designed to minimize changes to Main-Thermostat.cpp; all UI logic isolated here.
 */

#ifndef SETTINGS_UI_H
#define SETTINGS_UI_H

#include "TFT_Setup_ESP32_S3_Thermostat.h"
#include <Preferences.h>
#include <WiFi.h>

// Keyboard mode for reusing on-screen keyboard
enum KeyboardMode { KB_WIFI_SSID, KB_WIFI_PASS, KB_HOSTNAME };

// External references to main code objects (defined in Main-Thermostat.cpp)
extern LGFX tft;
extern Preferences preferences;

// External references to global settings (updated via UI)
extern float tempSwing;
extern float autoTempSwing;
extern bool fanRelayNeededHeat;
extern bool fanRelayNeededCool;
extern bool useFahrenheit;
extern unsigned long stage1MinRuntime;
extern float stage2TempDelta;
extern bool stage2HeatingEnabled;
extern bool stage2CoolingEnabled;
extern String hostname;
extern float currentTemp;
extern float currentHumidity;
extern bool forceFullDisplayRefresh;
extern bool inSettingsMenu;
extern bool inWiFiSetupMode;
extern bool keyboardReturnToSettings;
extern String inputText;
extern bool isUpperCaseKeyboard;
extern bool isEnteringSSID;

// External references to keyboard control (defined in Main)
extern KeyboardMode keyboardMode;

// External functions from Main
extern void saveSettings();
extern void updateDisplay(float temp, float hum);
extern void drawButtons();
extern void drawKeyboard(bool isUpperCase);
extern void setDisplayUpdateFlag();
extern void buzzerBeep(int duration);
extern void calibrateTouchScreen();
extern void runInteractiveCalibration();
extern void clearTouchCalibration();

// Color scheme (defined in main, redeclare for clarity)
#define COLOR_BACKGROUND   0x1082
#define COLOR_PRIMARY      0x1976
#define COLOR_SECONDARY    0x0497
#define COLOR_ACCENT       0xFFC1
#define COLOR_TEXT         0xFFFF
#define COLOR_TEXT_LIGHT   0xE0E0
#define COLOR_SUCCESS      0x4CAF
#define COLOR_WARNING      0xFF70
#define COLOR_SURFACE      0x2124

// Settings UI state
enum SettingsPage {
    PAGE_MENU,       // Main menu: WiFi, Comfort, HVAC Advanced, Hostname, System Info, Back
    PAGE_COMFORT,    // Temp swing, auto swing, fan relay, use F
    PAGE_HVAC_ADV,   // stage2 enable (heat/cool), stage1 min runtime, stage2 delta
    PAGE_HOSTNAME,   // Hostname entry (uses keyboard)
    PAGE_SYSINFO     // System information (IP, MAC, uptime, memory, etc)
};

// Current settings page
static SettingsPage currentPage = PAGE_MENU;

// Temporary edit buffer for numeric values
static float editTempSwing = 1.0;
static float editAutoTempSwing = 3.0;
static bool editFanRelayNeededHeat = false;
static bool editFanRelayNeededCool = false;
static bool editUseFahrenheit = true;
static unsigned long editStage1MinRuntime = 300;
static float editStage2TempDelta = 2.0;
static bool editStage2HeatingEnabled = false;
static bool editStage2CoolingEnabled = false;

// Forward declarations
void drawSettingsMenu();
void drawComfortSettings();
void drawHVACAdvancedSettings();
void drawSystemInfo();
bool settingsHandleTouch(uint16_t x, uint16_t y);
void enterSettingsMenu();
void exitSettingsToMain();
void startWiFiSetupUI(bool returnToSettings);
void startHostnameEntry();
void exitKeyboardToPreviousScreen();
void settingsLoopTick();

// Keep SettingsUI layout in a 320x240 virtual coordinate system.
static inline int settingsScaleX(int x) { return (x * dispW()) / 320; }
static inline int settingsScaleY(int y) { return (y * dispH()) / 240; }

// Helper: draw a labeled button
void drawSettingsButton(int x, int y, int w, int h, const char* label, uint16_t color) {
    int sx = settingsScaleX(x);
    int sy = settingsScaleY(y);
    int sw = settingsScaleX(w);
    int sh = settingsScaleY(h);
    tft.fillRect(sx, sy, sw, sh, color);
    tft.drawRect(sx, sy, sw, sh, COLOR_TEXT);
    tft.setTextColor(TFT_BLACK, color);
    tft.setTextSize(2);
    int textLen = strlen(label);
    int textWidth = textLen * 12; // approx for size 2
    int textX = sx + (sw - textWidth) / 2;
    int textY = sy + (sh - 16) / 2;
    tft.setCursor(textX, textY);
    tft.print(label);
}

// Helper: draw small toggle indicator
void drawToggle(int x, int y, bool state) {
    uint16_t toggleColor = state ? COLOR_SUCCESS : COLOR_WARNING;
    int sx = settingsScaleX(x);
    int sy = settingsScaleY(y);
    int r = settingsScaleX(10);
    tft.fillCircle(sx, sy, r, toggleColor);
    tft.drawCircle(sx, sy, r, COLOR_TEXT);
    tft.setTextColor(TFT_BLACK, toggleColor);
    tft.setTextSize(1);
    tft.setCursor(sx - settingsScaleX(6), sy - settingsScaleY(4));
    tft.print(state ? "ON" : "OFF");
}

// Helper: draw numeric value with +/- buttons
void drawNumericControl(int x, int y, const char* label, float value, int fieldId) {
    tft.setTextColor(COLOR_TEXT, COLOR_BACKGROUND);
    tft.setTextSize(2);
    tft.setCursor(settingsScaleX(x), settingsScaleY(y));
    tft.print(label);
    
    // - button
    int btnY = y + 25;
    tft.fillRect(settingsScaleX(x), settingsScaleY(btnY), settingsScaleX(30), settingsScaleY(30), COLOR_WARNING);
    tft.drawRect(settingsScaleX(x), settingsScaleY(btnY), settingsScaleX(30), settingsScaleY(30), COLOR_TEXT);
    tft.setTextColor(TFT_BLACK, COLOR_WARNING);
    tft.setCursor(settingsScaleX(x + 10), settingsScaleY(btnY + 8));
    tft.print("-");
    
    // Value display
    tft.setTextColor(COLOR_TEXT, COLOR_BACKGROUND);
    tft.setCursor(settingsScaleX(x + 35), settingsScaleY(btnY + 6));
    char buf[16];
    if (fieldId == 1 || fieldId == 2 || fieldId == 4) { // float fields
        snprintf(buf, sizeof(buf), "%.1f", value);
    } else { // unsigned long (stage1 runtime in seconds)
        snprintf(buf, sizeof(buf), "%lu", (unsigned long)value);
    }
    tft.print(buf);
    
    // + button
    tft.fillRect(settingsScaleX(x + 100), settingsScaleY(btnY), settingsScaleX(30), settingsScaleY(30), COLOR_SUCCESS);
    tft.drawRect(settingsScaleX(x + 100), settingsScaleY(btnY), settingsScaleX(30), settingsScaleY(30), COLOR_TEXT);
    tft.setTextColor(TFT_BLACK, COLOR_SUCCESS);
    tft.setCursor(settingsScaleX(x + 110), settingsScaleY(btnY + 8));
    tft.print("+");
}

// Enter settings menu from main screen
void enterSettingsMenu() {
    inSettingsMenu = true;
    currentPage = PAGE_MENU;
    
    // Load current values into edit buffers
    editTempSwing = tempSwing;
    editAutoTempSwing = autoTempSwing;
    editFanRelayNeededHeat = fanRelayNeededHeat;
    editFanRelayNeededCool = fanRelayNeededCool;
    editUseFahrenheit = useFahrenheit;
    editStage1MinRuntime = stage1MinRuntime;
    editStage2TempDelta = stage2TempDelta;
    editStage2HeatingEnabled = stage2HeatingEnabled;
    editStage2CoolingEnabled = stage2CoolingEnabled;
    
    drawSettingsMenu();
}

// Exit settings menu back to main display
void exitSettingsToMain() {
    inSettingsMenu = false;
    forceFullDisplayRefresh = true; // Ensure main UI fully redraws after exiting settings
    tft.fillScreen(COLOR_BACKGROUND);
    updateDisplay(currentTemp, currentHumidity);
    drawButtons();
}

// Draw main settings menu
void drawSettingsMenu() {
    tft.fillScreen(COLOR_BACKGROUND);
    tft.setTextColor(COLOR_TEXT, COLOR_BACKGROUND);
    tft.setTextSize(2);
    tft.setCursor(10, 10);
    tft.print("Settings Menu");
    
    // Menu buttons (2 columns to fit on screen)
    // Left column: x=20, Right column: x=170
    int btnW = 135, btnH = 40, spacing = 5;
    int leftX = 10, rightX = 165;
    int btnY = 50;
    
    // Row 1
    drawSettingsButton(leftX, btnY, btnW, btnH, "WiFi", COLOR_PRIMARY);
    drawSettingsButton(rightX, btnY, btnW, btnH, "Comfort", COLOR_SECONDARY);
    btnY += btnH + spacing;
    
    // Row 2
    drawSettingsButton(leftX, btnY, btnW, btnH, "HVAC Adv", COLOR_ACCENT);
    drawSettingsButton(rightX, btnY, btnW, btnH, "Hostname", COLOR_PRIMARY);
    btnY += btnH + spacing;
    
    // Row 3
    drawSettingsButton(leftX, btnY, btnW, btnH, "System", COLOR_SECONDARY);
    drawSettingsButton(rightX, btnY, btnW, btnH, "Back", COLOR_WARNING);
}

// Draw comfort settings page
void drawComfortSettings() {
    tft.fillScreen(COLOR_BACKGROUND);
    tft.setTextColor(COLOR_TEXT, COLOR_BACKGROUND);
    tft.setTextSize((dispW() > 320) ? 3 : 2);
    tft.setCursor(settingsScaleX(10), settingsScaleY(10));
    tft.print("Comfort Settings");
    
    int yPos = 30;
    
    // Temperature Swing
    drawNumericControl(20, yPos, "Temp Swing:", editTempSwing, 1);
    yPos += 60;
    
    // Auto Temp Swing
    drawNumericControl(20, yPos, "Auto Swing:", editAutoTempSwing, 2);
    yPos += 60;
    
    // Fan Relay Required for Heating toggle
    tft.setTextColor(COLOR_TEXT, COLOR_BACKGROUND);
    tft.setTextSize((dispW() > 320) ? 2 : 1);
    tft.setCursor(settingsScaleX(20), settingsScaleY(yPos));
    tft.print("Fan Relay Heat:");
    drawToggle(220, yPos + 5, editFanRelayNeededHeat);
    yPos += 18;

    // Fan Relay Required for Cooling toggle
    tft.setCursor(settingsScaleX(20), settingsScaleY(yPos));
    tft.print("Fan Relay Cool:");
    drawToggle(220, yPos + 5, editFanRelayNeededCool);
    yPos += 18;
    
    // Use Fahrenheit toggle
    tft.setCursor(settingsScaleX(20), settingsScaleY(yPos));
    tft.print("Use Fahrenheit:");
    drawToggle(220, yPos + 5, editUseFahrenheit);
    
    // Save and Back buttons
    drawSettingsButton(20, 200, 120, 35, "Save", COLOR_SUCCESS);
    drawSettingsButton(180, 200, 120, 35, "Back", COLOR_WARNING);
}

// Draw HVAC Advanced settings page
void drawHVACAdvancedSettings() {
    tft.fillScreen(COLOR_BACKGROUND);
    tft.setTextColor(COLOR_TEXT, COLOR_BACKGROUND);
    tft.setTextSize((dispW() > 320) ? 3 : 2);
    tft.setCursor(settingsScaleX(10), settingsScaleY(10));
    tft.print("HVAC Advanced");
    
    int yPos = 30;
    
    // Stage1 Min Runtime (seconds)
    drawNumericControl(20, yPos, "Stage1 Min (s):", (float)editStage1MinRuntime, 3);
    yPos += 60;
    
    // Stage2 Temp Delta
    drawNumericControl(20, yPos, "Stage2 Delta:", editStage2TempDelta, 4);
    yPos += 60;
    
    // Stage2 Heat Enable toggle
    tft.setTextColor(COLOR_TEXT, COLOR_BACKGROUND);
    tft.setTextSize((dispW() > 320) ? 2 : 1);
    tft.setCursor(settingsScaleX(20), settingsScaleY(yPos));
    tft.print("Stage2 Heat Enable:");
    drawToggle(220, yPos + 5, editStage2HeatingEnabled);
    yPos += 18;
    
    // Stage2 Cool Enable toggle
    tft.setCursor(settingsScaleX(20), settingsScaleY(yPos));
    tft.print("Stage2 Cool Enable:");
    drawToggle(220, yPos + 5, editStage2CoolingEnabled);
    
    // Save and Back buttons
    drawSettingsButton(20, 200, 120, 35, "Save", COLOR_SUCCESS);
    drawSettingsButton(180, 200, 120, 35, "Back", COLOR_WARNING);
}

// Draw System Info page
void drawSystemInfo() {
    tft.fillScreen(COLOR_BACKGROUND);
    tft.setTextColor(COLOR_TEXT, COLOR_BACKGROUND);
    tft.setTextSize(2);
    tft.setCursor(10, 10);
    tft.print("System Info");
    
    tft.setTextSize(1);
    int yPos = 40;
    
    // IP Address
    tft.setCursor(10, yPos);
    tft.print("IP: ");
    tft.print(WiFi.localIP().toString());
    yPos += 15;
    
    // MAC Address
    tft.setCursor(10, yPos);
    tft.print("MAC: ");
    tft.print(WiFi.macAddress());
    yPos += 15;
    
    // Hostname
    tft.setCursor(10, yPos);
    tft.print("Hostname: ");
    tft.print(hostname);
    yPos += 15;
    
    // WiFi SSID
    tft.setCursor(10, yPos);
    tft.print("SSID: ");
    tft.print(WiFi.SSID());
    yPos += 15;
    
    // WiFi Signal Strength
    tft.setCursor(10, yPos);
    tft.print("RSSI: ");
    tft.print(WiFi.RSSI());
    tft.print(" dBm");
    yPos += 20;
    
    // Uptime
    unsigned long uptimeSeconds = millis() / 1000;
    unsigned long days = uptimeSeconds / 86400;
    unsigned long hours = (uptimeSeconds % 86400) / 3600;
    unsigned long minutes = (uptimeSeconds % 3600) / 60;
    unsigned long seconds = uptimeSeconds % 60;
    
    tft.setCursor(10, yPos);
    tft.print("Uptime: ");
    tft.print(days);
    tft.print("d ");
    tft.print(hours);
    tft.print("h ");
    tft.print(minutes);
    tft.print("m ");
    tft.print(seconds);
    tft.print("s");
    yPos += 20;
    
    // Free Heap
    tft.setCursor(10, yPos);
    tft.print("Free Heap: ");
    tft.print(ESP.getFreeHeap());
    tft.print(" bytes");
    yPos += 15;
    
    // Chip Model
    tft.setCursor(10, yPos);
    tft.print("Chip: ");
    tft.print(ESP.getChipModel());
    yPos += 15;
    
    // Chip Revision
    tft.setCursor(10, yPos);
    tft.print("Revision: ");
    tft.print(ESP.getChipRevision());
    yPos += 15;
    
    // CPU Frequency
    tft.setCursor(10, yPos);
    tft.print("CPU Freq: ");
    tft.print(ESP.getCpuFreqMHz());
    tft.print(" MHz");
    yPos += 15;
    
    // Flash Size
    tft.setCursor(10, yPos);
    tft.print("Flash: ");
    tft.print(ESP.getFlashChipSize() / (1024 * 1024));
    tft.print(" MB");
    
    // Calibrate, Clear Cal, and Back buttons (right side)
    drawSettingsButton(213, 80, 95, 35, "Calibrate", COLOR_PRIMARY);
    drawSettingsButton(213, 125, 95, 35, "Clear Cal", TFT_RED);
    drawSettingsButton(213, 170, 95, 35, "Back", COLOR_WARNING);
}

// Launch WiFi setup (reuse existing keyboard flow)
void startWiFiSetupUI(bool returnToSettings) {
    keyboardReturnToSettings = returnToSettings;
    inWiFiSetupMode = true;
    inputText = "";
    isEnteringSSID = true;
    keyboardMode = (KeyboardMode)0; // KB_WIFI_SSID
    
    tft.fillScreen(COLOR_BACKGROUND);
    drawKeyboard(isUpperCaseKeyboard);
}

// Launch hostname entry (keyboard mode)
void startHostnameEntry() {
    inWiFiSetupMode = true;
    inputText = hostname; // pre-fill current hostname
    keyboardMode = (KeyboardMode)2; // KB_HOSTNAME
    keyboardReturnToSettings = true;
    
    tft.fillScreen(COLOR_BACKGROUND);
    drawKeyboard(isUpperCaseKeyboard);
}

// Exit keyboard back to previous screen (main or settings)
void exitKeyboardToPreviousScreen() {
    inWiFiSetupMode = false;
    
    if (keyboardReturnToSettings) {
        // Return to settings menu
        inSettingsMenu = true;
        drawSettingsMenu();
        keyboardReturnToSettings = false;
    } else {
        // Return to main display
        exitSettingsToMain();
    }
}

// Handle touch events when settings UI is active
bool settingsHandleTouch(uint16_t x, uint16_t y) {
    buzzerBeep(50);
    
    // Main settings menu
    if (currentPage == PAGE_MENU) {
        int btnW = 135, btnH = 40, spacing = 5;
        int leftX = 10, rightX = 165;
        int btnY = 50;
        
        // Row 1: WiFi (left) and Comfort (right)
        if (y >= btnY && y <= btnY + btnH) {
            if (x >= leftX && x <= leftX + btnW) {
                // WiFi button
                startWiFiSetupUI(true);
                return true;
            } else if (x >= rightX && x <= rightX + btnW) {
                // Comfort button
                currentPage = PAGE_COMFORT;
                drawComfortSettings();
                return true;
            }
        }
        btnY += btnH + spacing;
        
        // Row 2: HVAC Advanced (left) and Hostname (right)
        if (y >= btnY && y <= btnY + btnH) {
            if (x >= leftX && x <= leftX + btnW) {
                // HVAC Advanced button
                currentPage = PAGE_HVAC_ADV;
                drawHVACAdvancedSettings();
                return true;
            } else if (x >= rightX && x <= rightX + btnW) {
                // Hostname button
                startHostnameEntry();
                return true;
            }
        }
        btnY += btnH + spacing;
        
        // Row 3: System Info (left) and Back (right)
        if (y >= btnY && y <= btnY + btnH) {
            if (x >= leftX && x <= leftX + btnW) {
                // System Info button
                currentPage = PAGE_SYSINFO;
                drawSystemInfo();
                return true;
            } else if (x >= rightX && x <= rightX + btnW) {
                // Back to Main button
                exitSettingsToMain();
                return true;
            }
        }
    }
    
    // Comfort settings page
    else if (currentPage == PAGE_COMFORT) {
        int yPos = 30;
        
        // Temp Swing +/-
        if (y >= yPos + 25 && y <= yPos + 55) {
            if (x >= 20 && x <= 50) { // - button
                editTempSwing -= 0.1;
                if (editTempSwing < 0.2) editTempSwing = 0.2;
                drawComfortSettings();
                return true;
            } else if (x >= 120 && x <= 150) { // + button
                editTempSwing += 0.1;
                if (editTempSwing > 3.0) editTempSwing = 3.0;
                drawComfortSettings();
                return true;
            }
        }
        yPos += 60;
        
        // Auto Temp Swing +/-
        if (y >= yPos + 25 && y <= yPos + 55) {
            if (x >= 20 && x <= 50) { // - button
                editAutoTempSwing -= 0.1;
                if (editAutoTempSwing < 0.2) editAutoTempSwing = 0.2;
                drawComfortSettings();
                return true;
            } else if (x >= 120 && x <= 150) { // + button
                editAutoTempSwing += 0.1;
                if (editAutoTempSwing > 5.0) editAutoTempSwing = 5.0;
                drawComfortSettings();
                return true;
            }
        }
        yPos += 60;
        
        // Fan Relay Heat toggle
        if (x >= 200 && x <= 240 && y >= yPos && y <= yPos + 20) {
            editFanRelayNeededHeat = !editFanRelayNeededHeat;
            drawComfortSettings();
            return true;
        }
        yPos += 20;

        // Fan Relay Cool toggle
        if (x >= 200 && x <= 240 && y >= yPos && y <= yPos + 20) {
            editFanRelayNeededCool = !editFanRelayNeededCool;
            drawComfortSettings();
            return true;
        }
        yPos += 20;
        
        // Use Fahrenheit toggle
        if (x >= 200 && x <= 240 && y >= yPos && y <= yPos + 20) {
            editUseFahrenheit = !editUseFahrenheit;
            drawComfortSettings();
            return true;
        }
        
        // Save button
        if (x >= 20 && x <= 140 && y >= 200 && y <= 235) {
            tempSwing = editTempSwing;
            autoTempSwing = editAutoTempSwing;
            fanRelayNeededHeat = editFanRelayNeededHeat;
            fanRelayNeededCool = editFanRelayNeededCool;
            useFahrenheit = editUseFahrenheit;
            saveSettings();
            setDisplayUpdateFlag();
            currentPage = PAGE_MENU;
            drawSettingsMenu();
            return true;
        }
        
        // Back button
        if (x >= 180 && x <= 300 && y >= 200 && y <= 235) {
            // Discard changes
            currentPage = PAGE_MENU;
            drawSettingsMenu();
            return true;
        }
    }
    
    // HVAC Advanced settings page
    else if (currentPage == PAGE_HVAC_ADV) {
        int yPos = 30;
        
        // Stage1 Min Runtime +/-
        if (y >= yPos + 25 && y <= yPos + 55) {
            if (x >= 20 && x <= 50) { // - button
                if (editStage1MinRuntime > 60) editStage1MinRuntime -= 30;
                drawHVACAdvancedSettings();
                return true;
            } else if (x >= 120 && x <= 150) { // + button
                if (editStage1MinRuntime < 1800) editStage1MinRuntime += 30;
                drawHVACAdvancedSettings();
                return true;
            }
        }
        yPos += 60;
        
        // Stage2 Temp Delta +/-
        if (y >= yPos + 25 && y <= yPos + 55) {
            if (x >= 20 && x <= 50) { // - button
                editStage2TempDelta -= 0.5;
                if (editStage2TempDelta < 0.5) editStage2TempDelta = 0.5;
                drawHVACAdvancedSettings();
                return true;
            } else if (x >= 120 && x <= 150) { // + button
                editStage2TempDelta += 0.5;
                if (editStage2TempDelta > 5.0) editStage2TempDelta = 5.0;
                drawHVACAdvancedSettings();
                return true;
            }
        }
        yPos += 60;
        
        // Stage2 Heat Enable toggle
        if (x >= 200 && x <= 240 && y >= yPos && y <= yPos + 20) {
            editStage2HeatingEnabled = !editStage2HeatingEnabled;
            drawHVACAdvancedSettings();
            return true;
        }
        yPos += 20;
        
        // Stage2 Cool Enable toggle
        if (x >= 200 && x <= 240 && y >= yPos && y <= yPos + 20) {
            editStage2CoolingEnabled = !editStage2CoolingEnabled;
            drawHVACAdvancedSettings();
            return true;
        }
        
        // Save button
        if (x >= 20 && x <= 140 && y >= 200 && y <= 235) {
            stage1MinRuntime = editStage1MinRuntime;
            stage2TempDelta = editStage2TempDelta;
            stage2HeatingEnabled = editStage2HeatingEnabled;
            stage2CoolingEnabled = editStage2CoolingEnabled;
            saveSettings();
            setDisplayUpdateFlag();
            currentPage = PAGE_MENU;
            drawSettingsMenu();
            return true;
        }
        
        // Back button
        if (x >= 180 && x <= 300 && y >= 200 && y <= 235) {
            // Discard changes
            currentPage = PAGE_MENU;
            drawSettingsMenu();
            return true;
        }
    }
    
    // System Info page
    else if (currentPage == PAGE_SYSINFO) {
        // Calibrate button (top right)
        if (x >= 213 && x <= 308 && y >= 80 && y <= 115) {
            runInteractiveCalibration();
            // After calibration completes, redraw the system info page
            drawSystemInfo();
            return true;
        }
        // Clear Cal button (middle right)
        else if (x >= 213 && x <= 308 && y >= 125 && y <= 160) {
            clearTouchCalibration();
            // Note: clearTouchCalibration() will reboot the device
            return true;
        }
        // Back button (bottom right)
        else if (x >= 213 && x <= 308 && y >= 170 && y <= 205) {
            currentPage = PAGE_MENU;
            drawSettingsMenu();
            return true;
        }
    }
    
    return false;
}

// Loop tick when settings UI is active (currently no background work needed)
void settingsLoopTick() {
    // Placeholder for any periodic updates while in settings
    // For now, settings is purely event-driven (touch-based)
}

#endif // SETTINGS_UI_H
